jsjolund/sailoraid/report/Figures/Euler_angle.pdf

Yaw

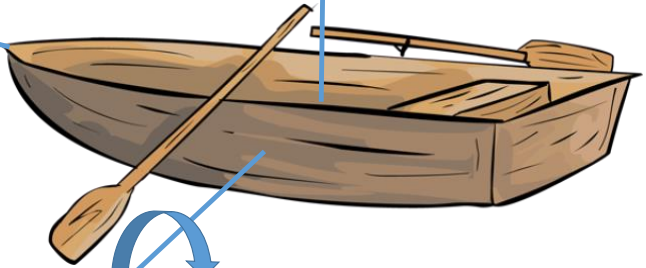
[picture p74: figure]

Pitch

Roll
