jsjolund/sailoraid/report/SourceFigures/linear.pdf

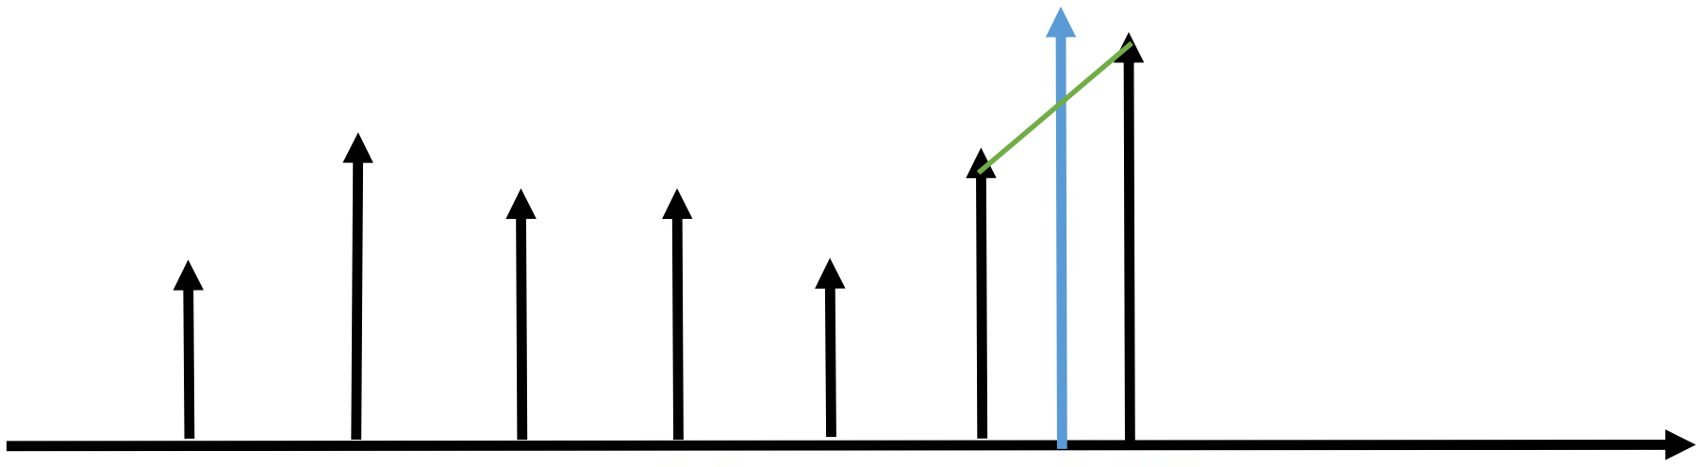
[picture p75: figure]
