jsjolund/sailoraid/Hardware/Mountingstation/Size of PCB.png

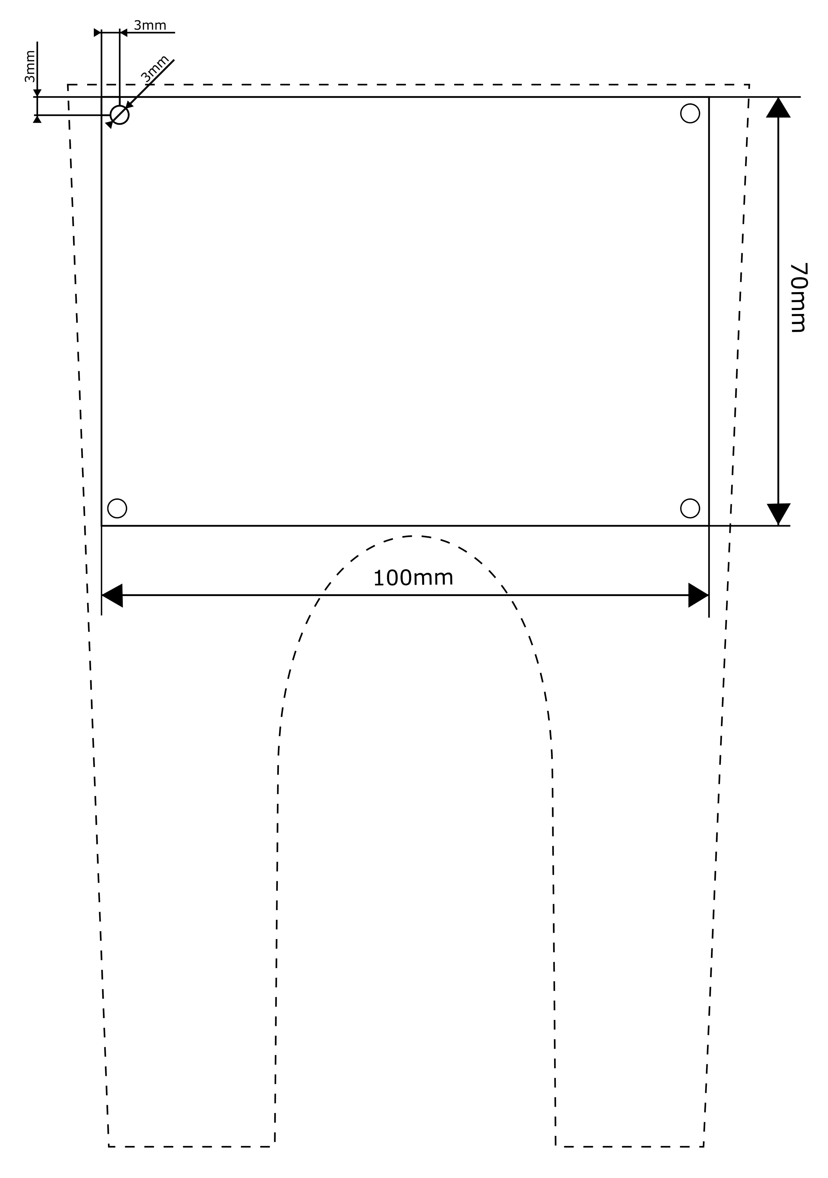
Hardware/Mountingstation/Size of PCB.png
