jsjolund/sailoraid/Presentationer/9/PCB_rev2_0.0.1.png

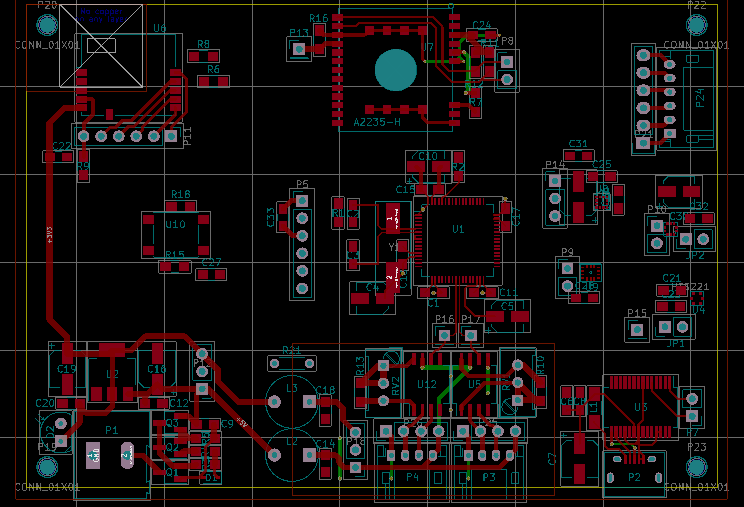
Presentationer/9/PCB_rev2_0.0.1.png
