jsjolund/sailoraid/Presentationer/11/pcb_rev2_Cu_tight.png

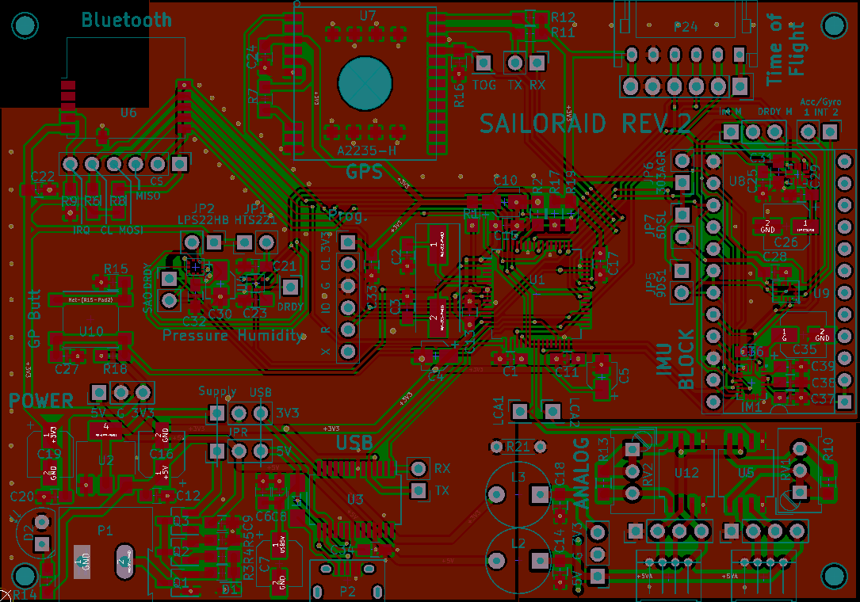
Presentationer/11/pcb_rev2_Cu_tight.png
