jsjolund/sailoraid/Presentationer/11/pcb_rev2_NoCu.png

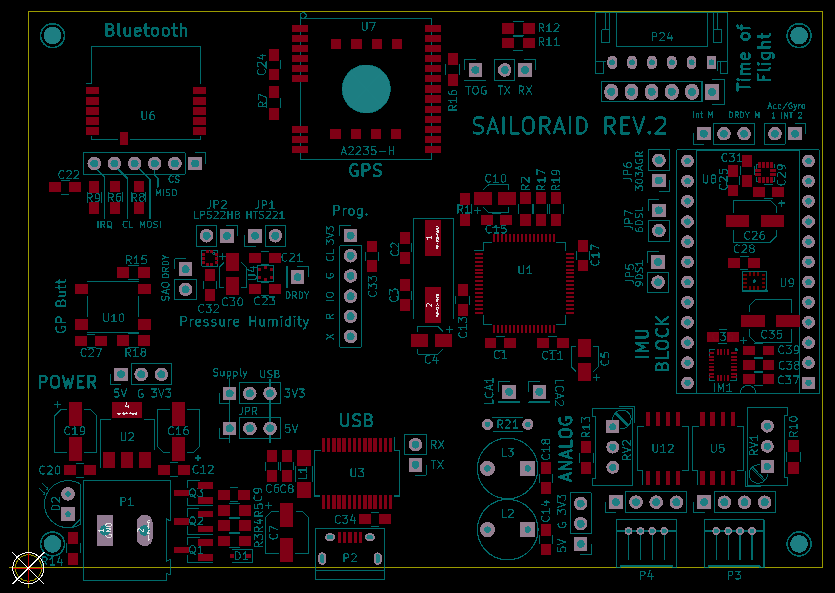
Presentationer/11/pcb_rev2_NoCu.png
