jsjolund/sailoraid/Presentationer/11/pcb_rev2_NoCu_decisions.png

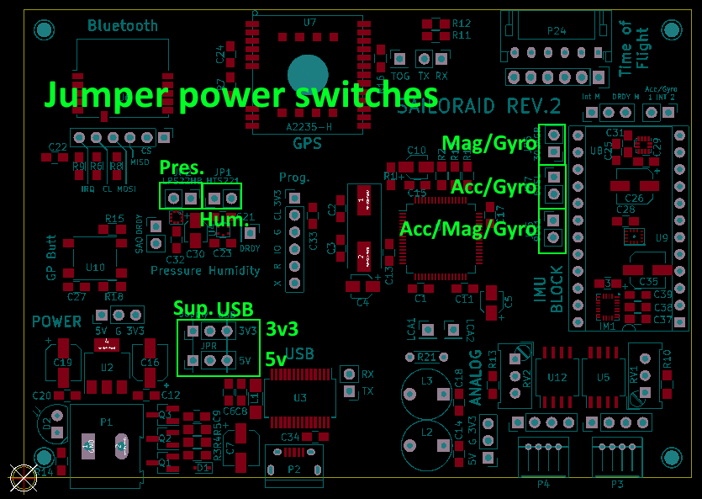
Presentationer/11/pcb_rev2_NoCu_decisions.png
