jsjolund/sailoraid/Presentationer/11/pcb_rev2_NoCu_eval.png

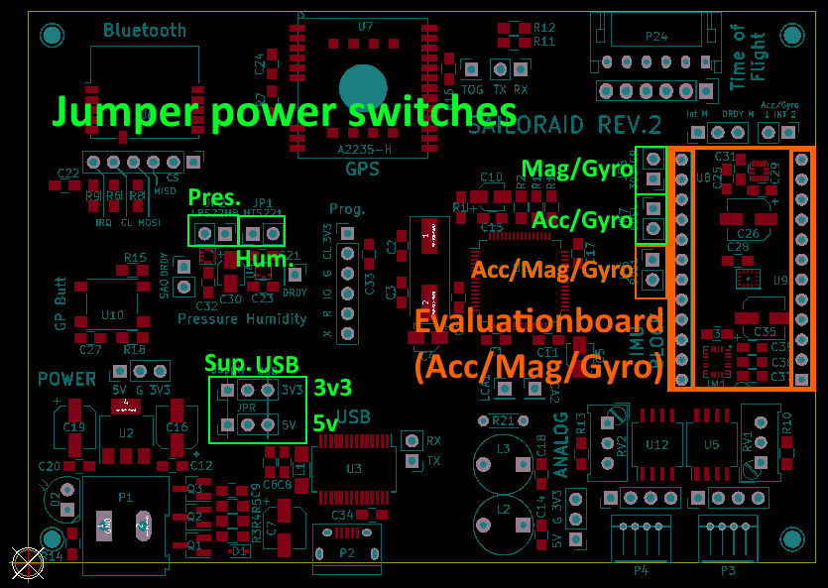
Presentationer/11/pcb_rev2_NoCu_eval.png
