jsjolund/sailoraid/Presentationer/11/pcb_rev2_NoCu_Marks.png

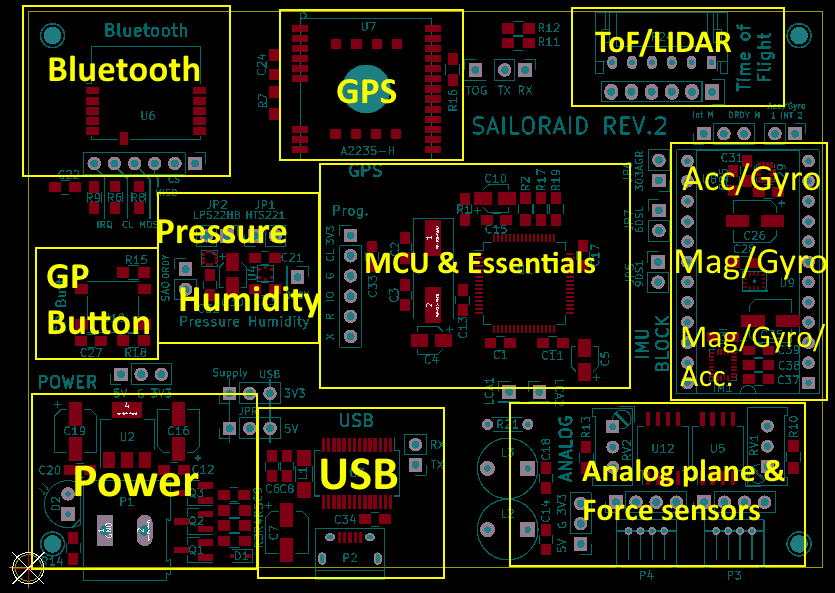
Presentationer/11/pcb_rev2_NoCu_Marks.png
