jsjolund/sailoraid/Presentationer/11/pcb_rev2_NoCu_meas.png

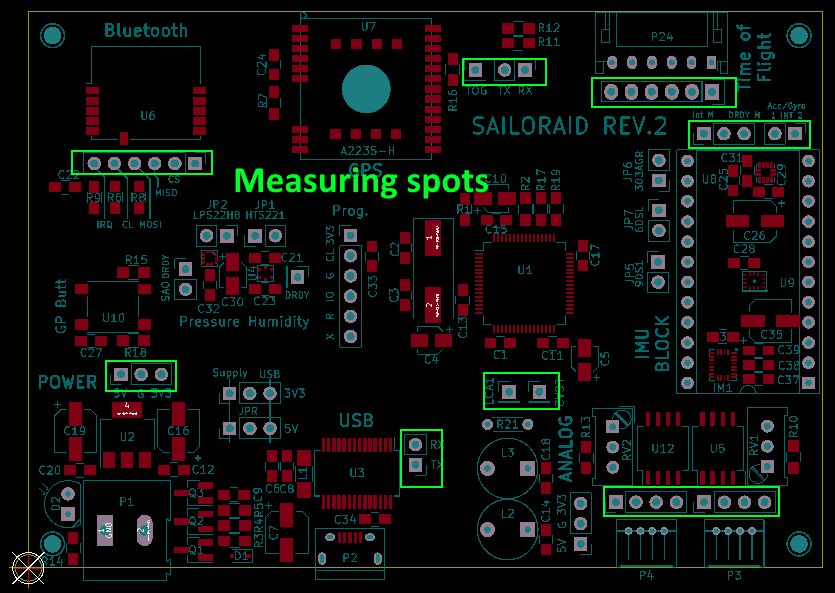
Presentationer/11/pcb_rev2_NoCu_meas.png
