jsjolund/sailoraid/Presentationer/11/pcb_rev2_NoCu_noeval.png

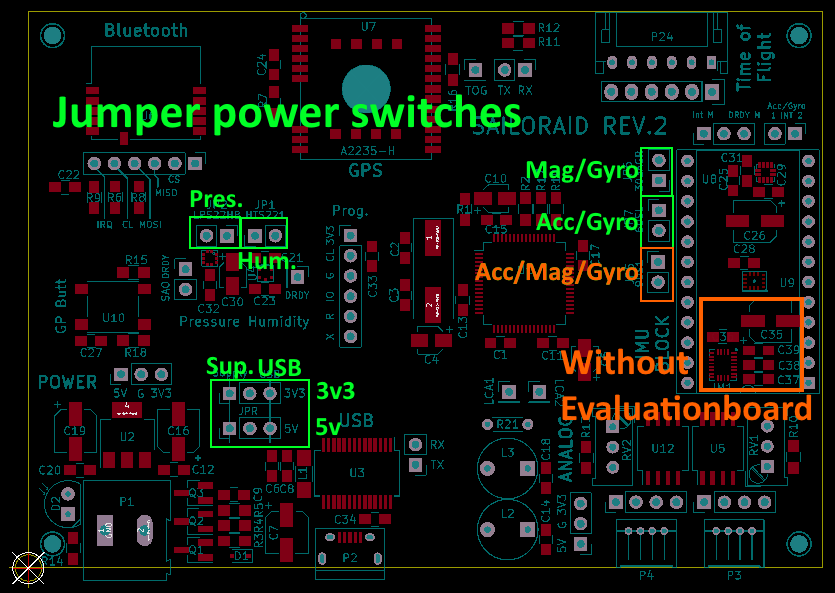
Presentationer/11/pcb_rev2_NoCu_noeval.png
