jsjolund/sailoraid/Presentationer/11/rev2_fitted.png

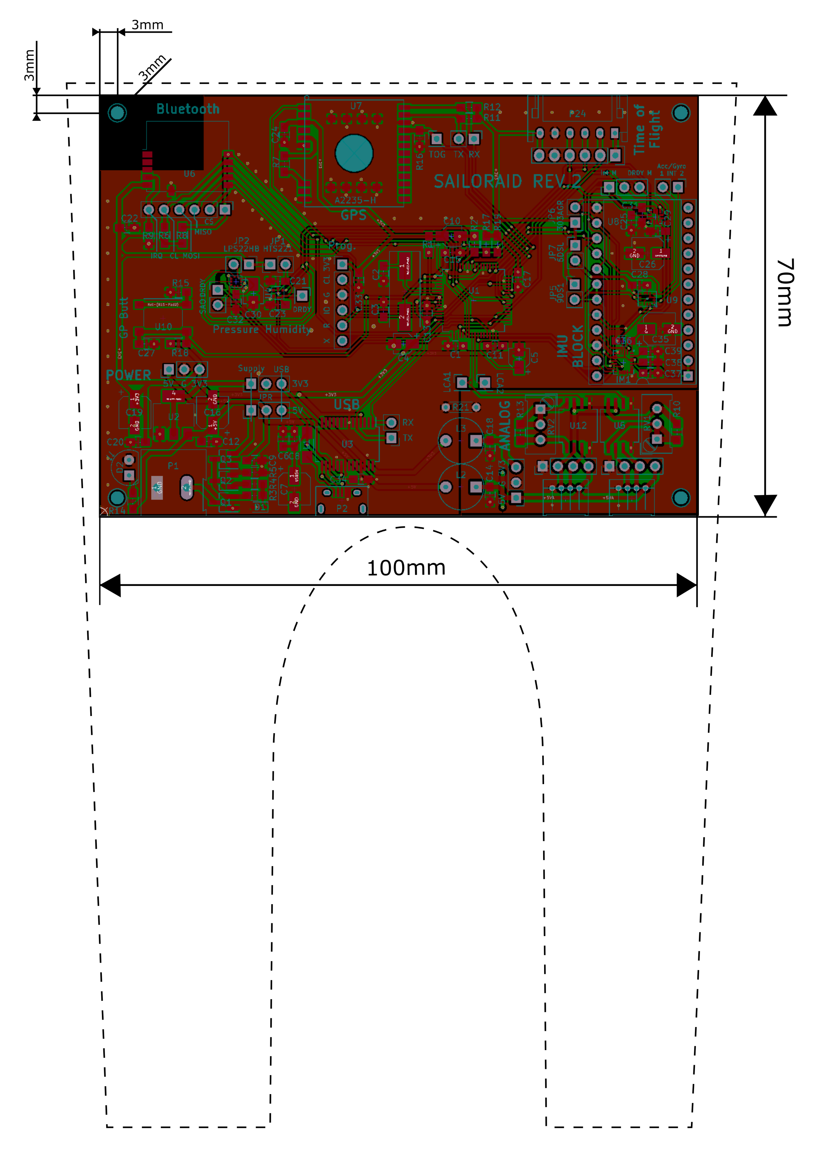
Presentationer/11/rev2_fitted.png
