jsjolund/sailoraid/Presentationer/Presentation 4/PCB_Annotated.png

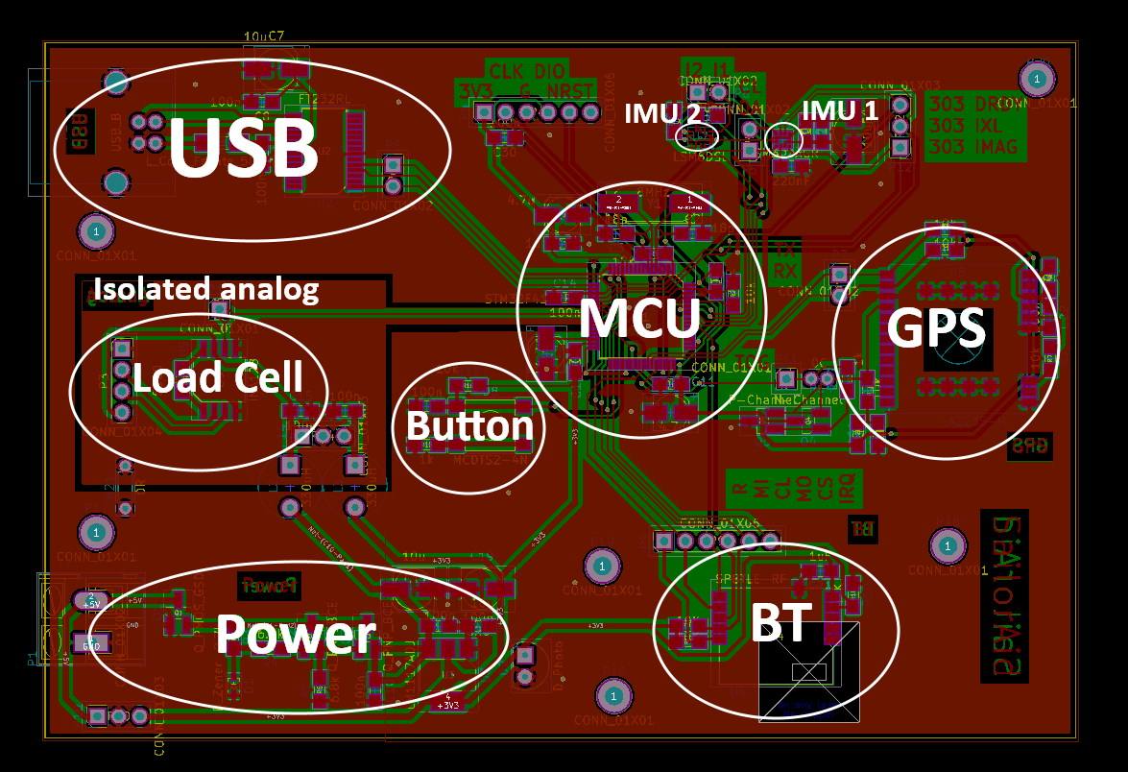
Presentationer/Presentation 4/PCB_Annotated.png
