jsjolund/sailoraid/Presentationer/Presentation 4/PCB_BAT_Note.png

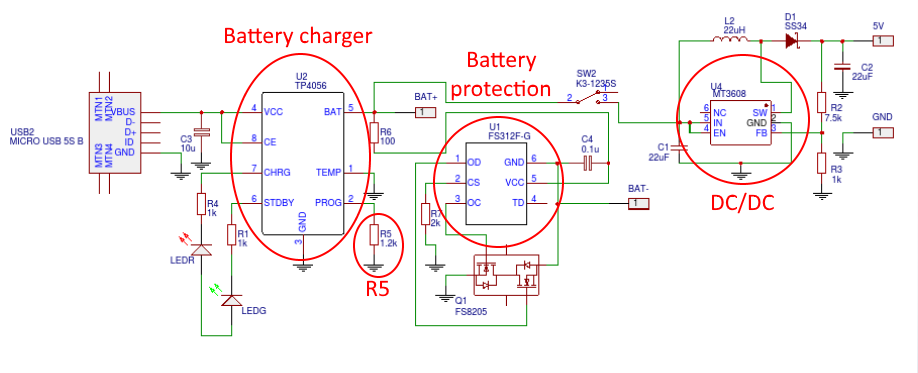
Presentationer/Presentation 4/PCB_BAT_Note.png
