jsjolund/sailoraid/Presentationer/Presentation 4/PCB_TN.png

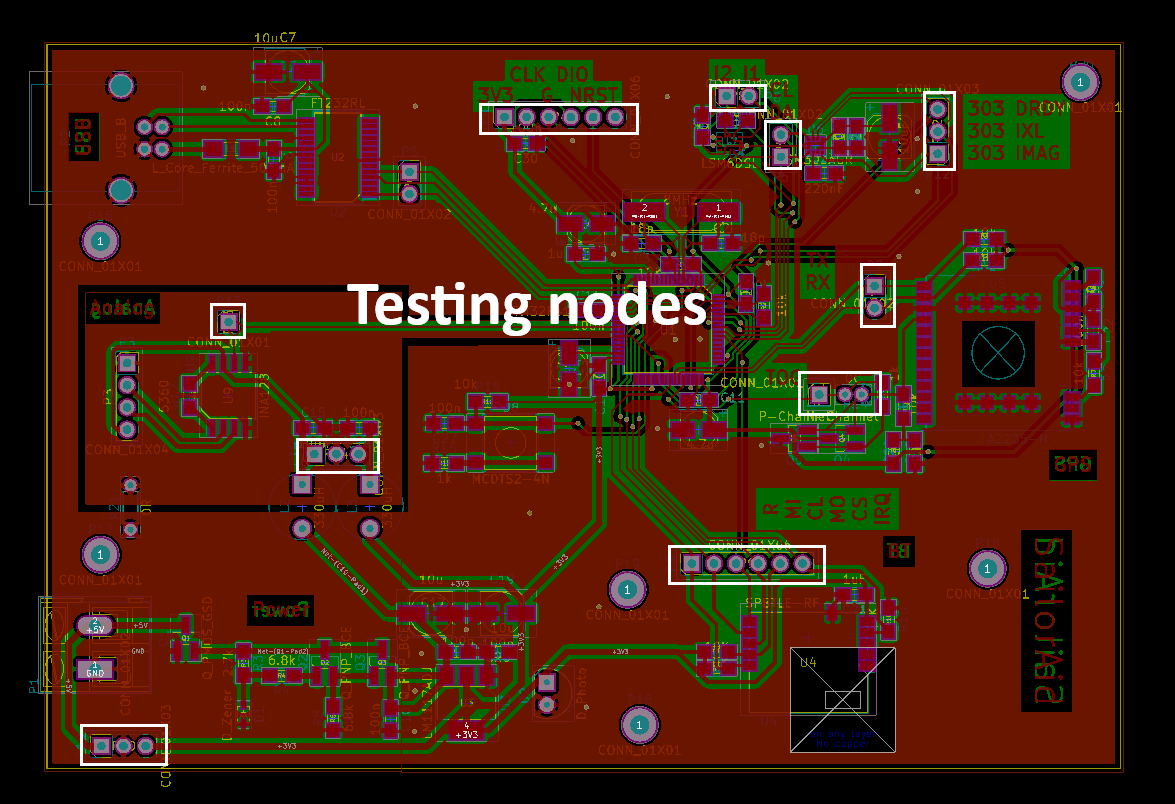
Presentationer/Presentation 4/PCB_TN.png
