jsjolund/sailoraid/Presentationer/Presentation 4/PCB_View.png

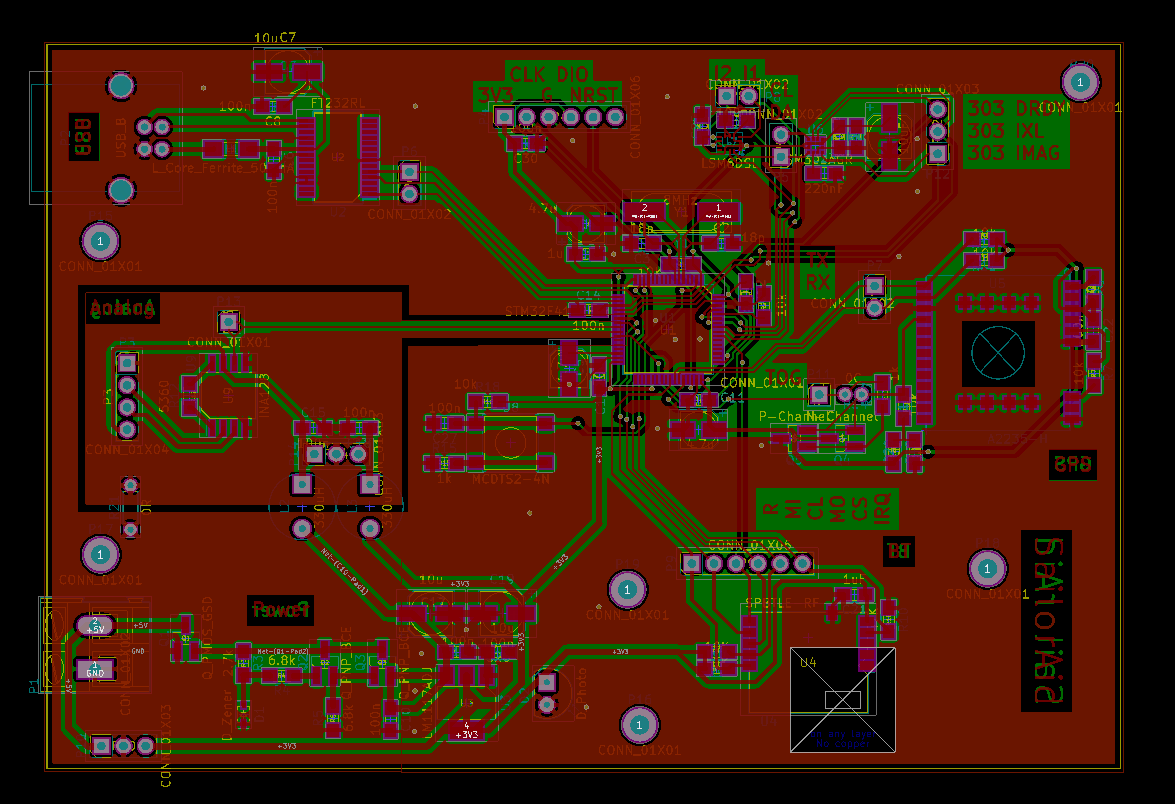
Presentationer/Presentation 4/PCB_View.png
