jsjolund/sailoraid/Presentationer/Presentation 4/schematic_General.png

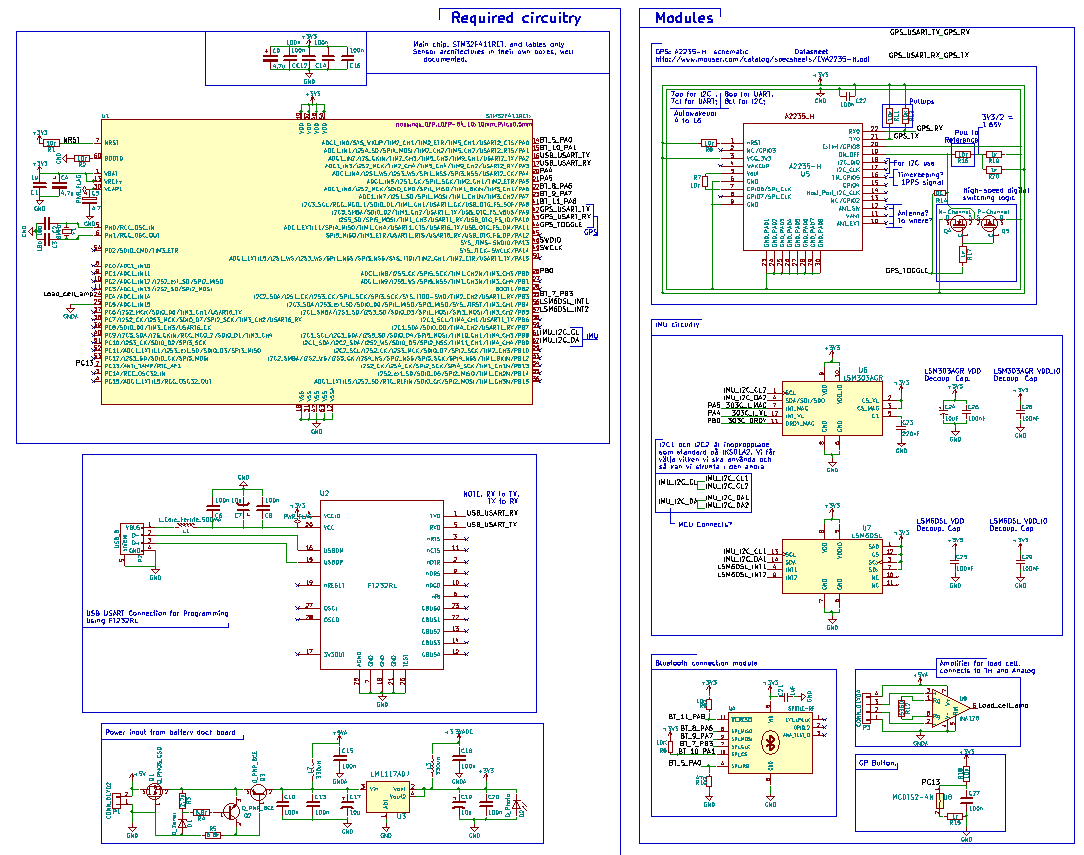
Presentationer/Presentation 4/schematic_General.png
