jsjolund/sailoraid/Presentationer/Presentation 4/schematic_General_note.png

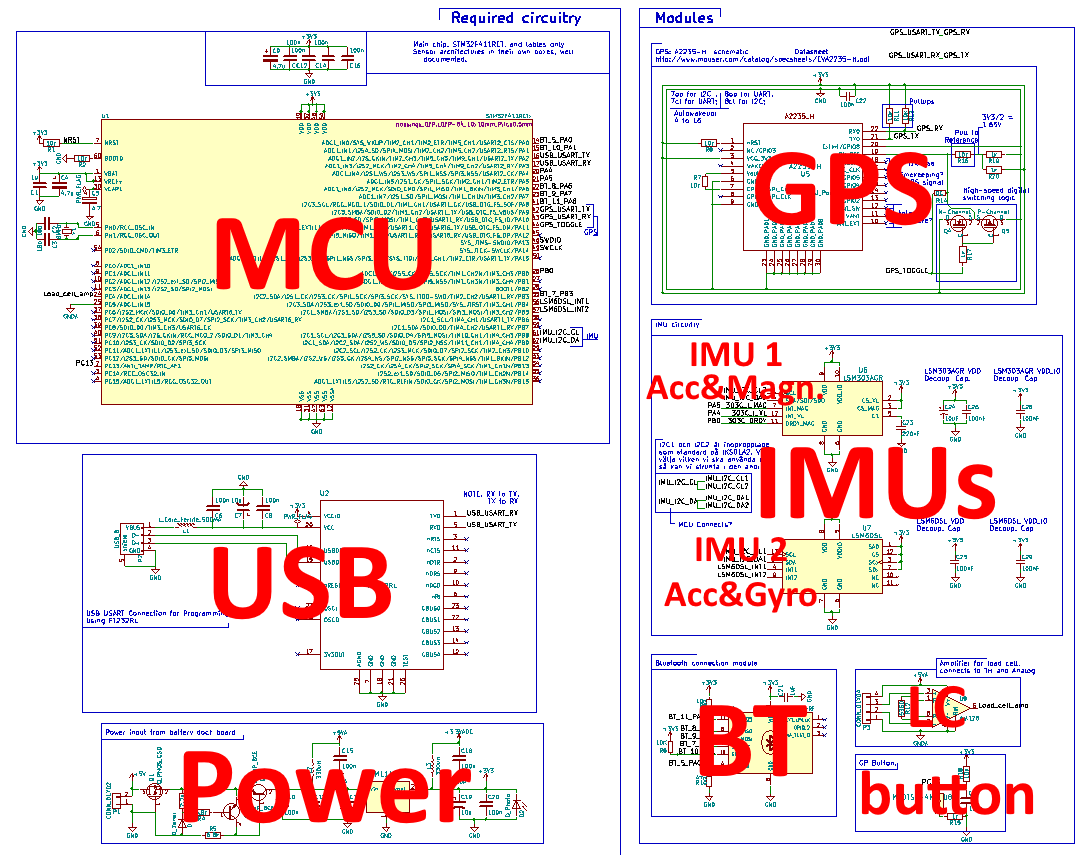
Presentationer/Presentation 4/schematic_General_note.png
