jsjolund/sailoraid/Presentationer/Presentation 4/schematic_MN.png

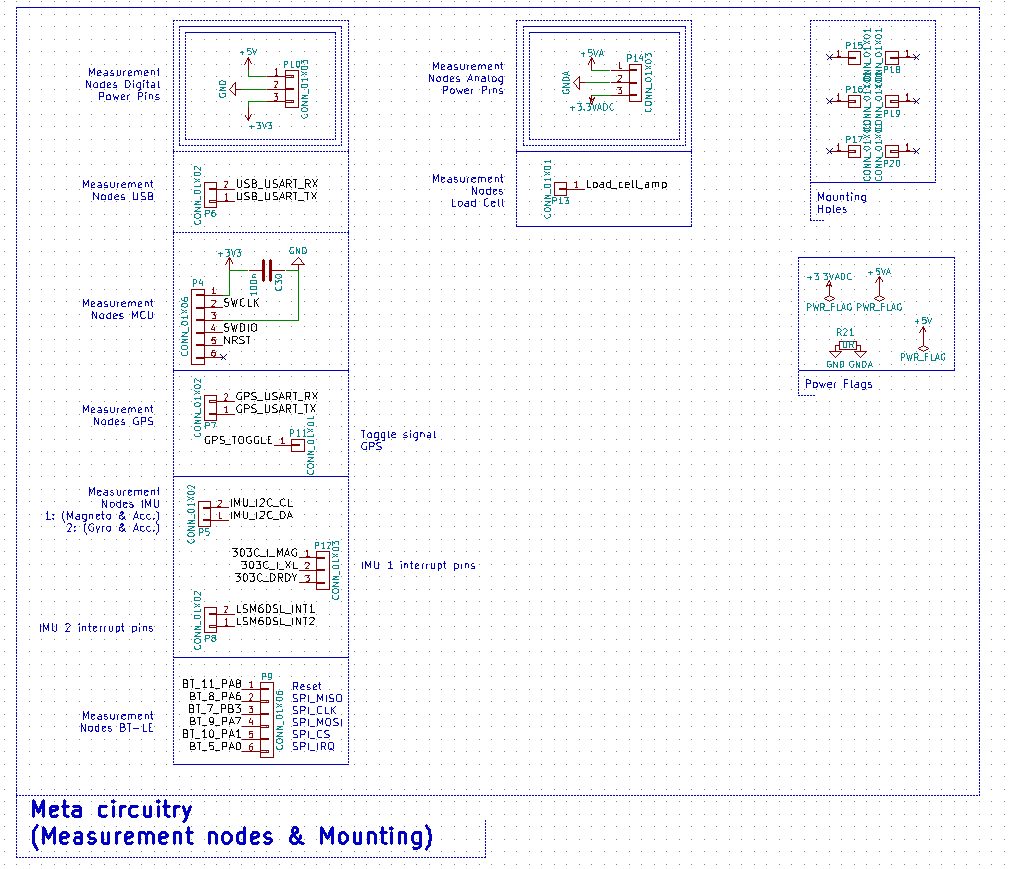
Presentationer/Presentation 4/schematic_MN.png
