jsjolund/sailoraid/Presentationer/Presentation 6/img/22359539_10154808777265474_2147093659_n.jpg

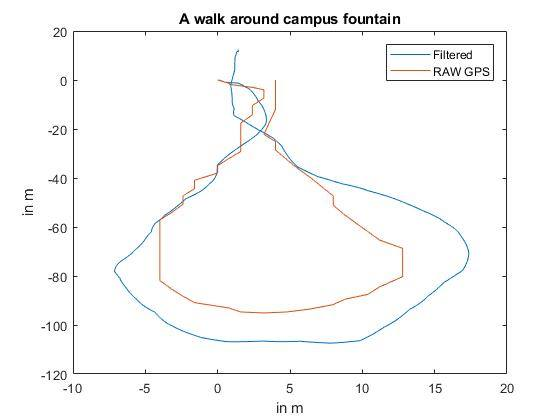
Presentationer/Presentation 6/img/22359539_10154808777265474_2147093659_n.jpg
