jsjolund/sailoraid/Presentationer/Presentation 6/img/log.png

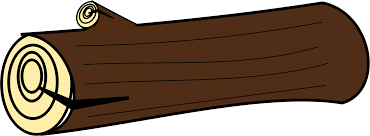
Presentationer/Presentation 6/img/log.png
