jsjolund/sailoraid/Presentationer/Presentation 6/img/low-battery-white-outline.png

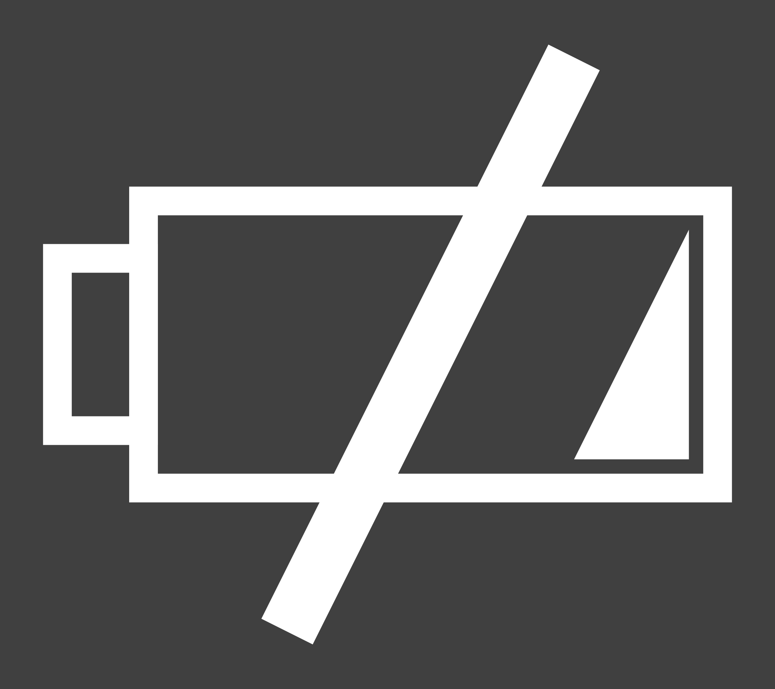
Presentationer/Presentation 6/img/low-battery-white-outline.png
