jsjolund/sailoraid/Presentationer/Presentation 6/img/Screenshot_20171006-211432.png

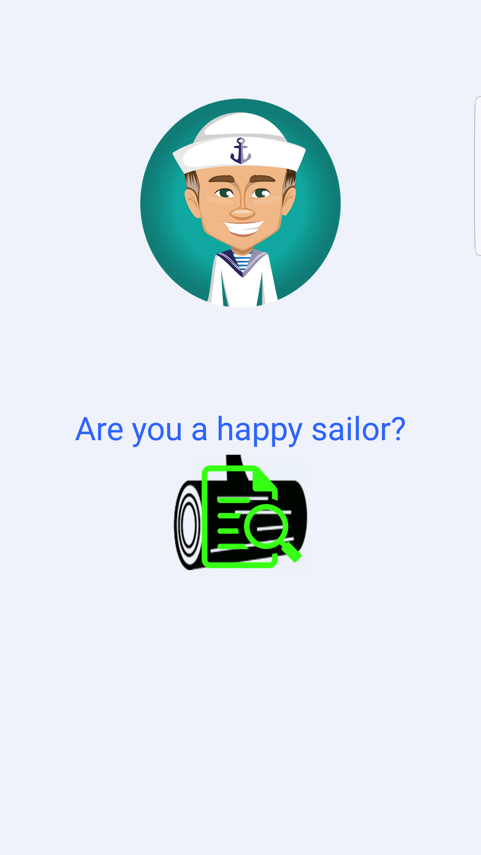
Presentationer/Presentation 6/img/Screenshot_20171006-211432.png
