jsjolund/sailoraid/Presentationer/Presentation 6/img/Screenshot_20171006-211447.png

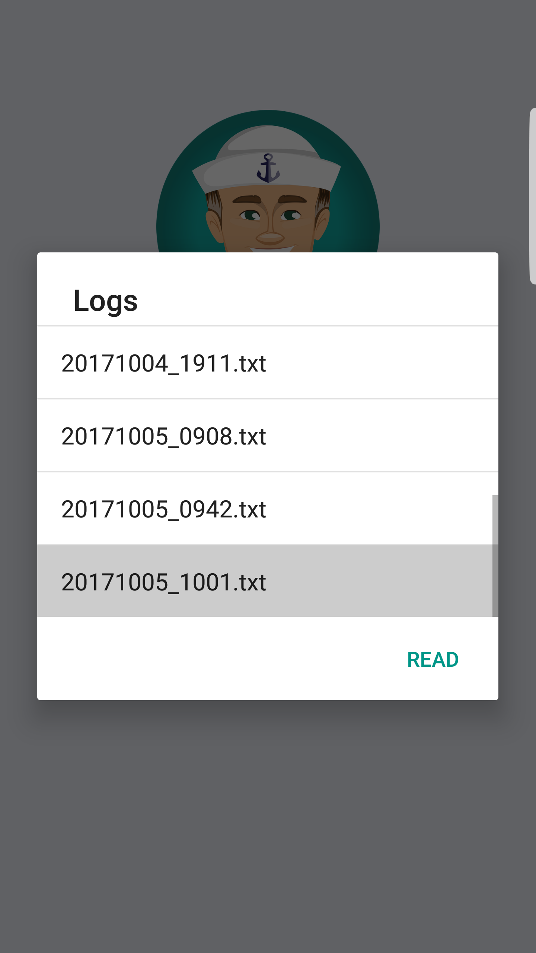
Presentationer/Presentation 6/img/Screenshot_20171006-211447.png
