jsjolund/sailoraid/Presentationer/Presentation 6/img/Screenshot_20171006-212822.png

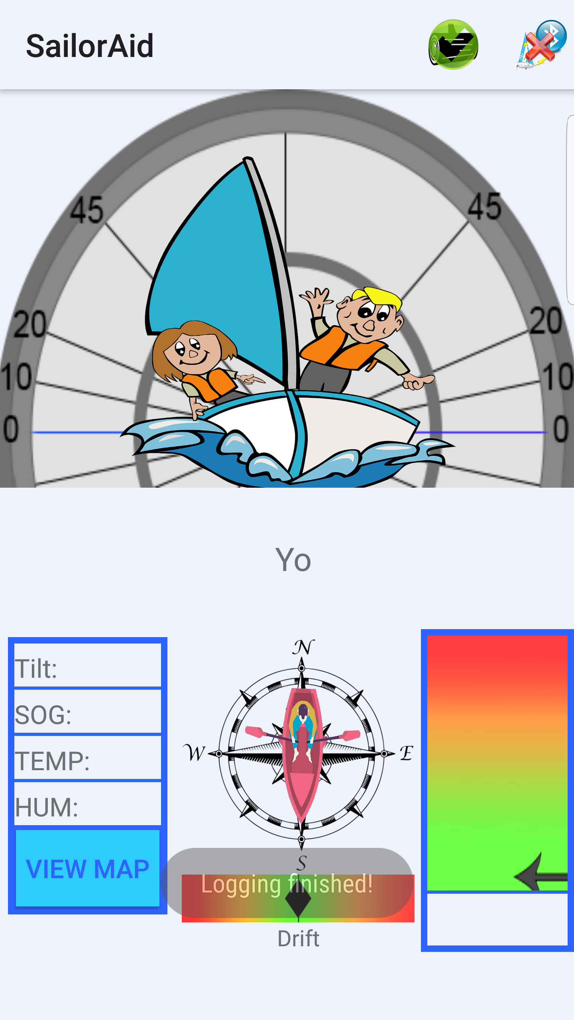
Presentationer/Presentation 6/img/Screenshot_20171006-212822.png
