jsjolund/sailoraid/Presentationer/Presentation 6/img/Screenshot_20171006-213508.png

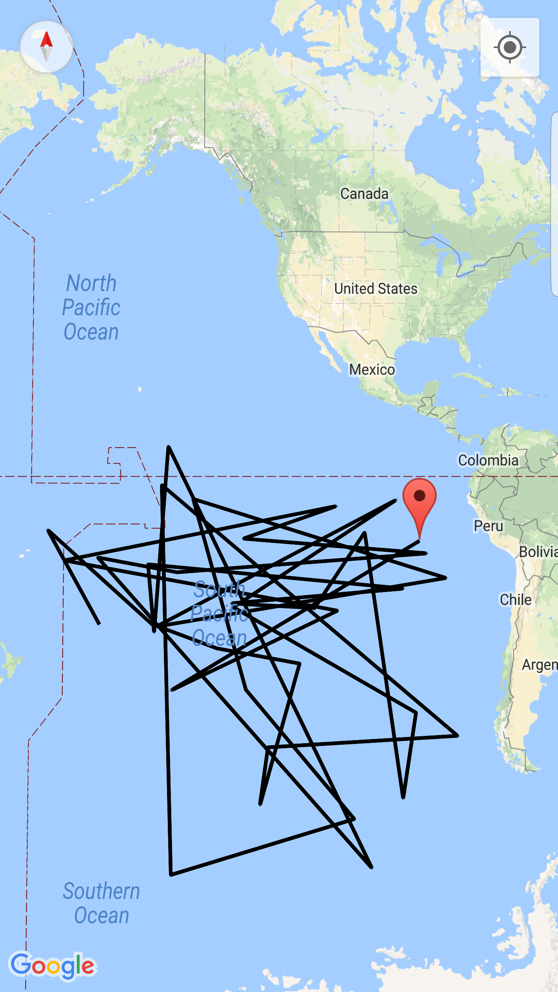
Presentationer/Presentation 6/img/Screenshot_20171006-213508.png
