jsjolund/sailoraid/Presentationer/Presentation 6/img/Screenshot_20171006-220036.png

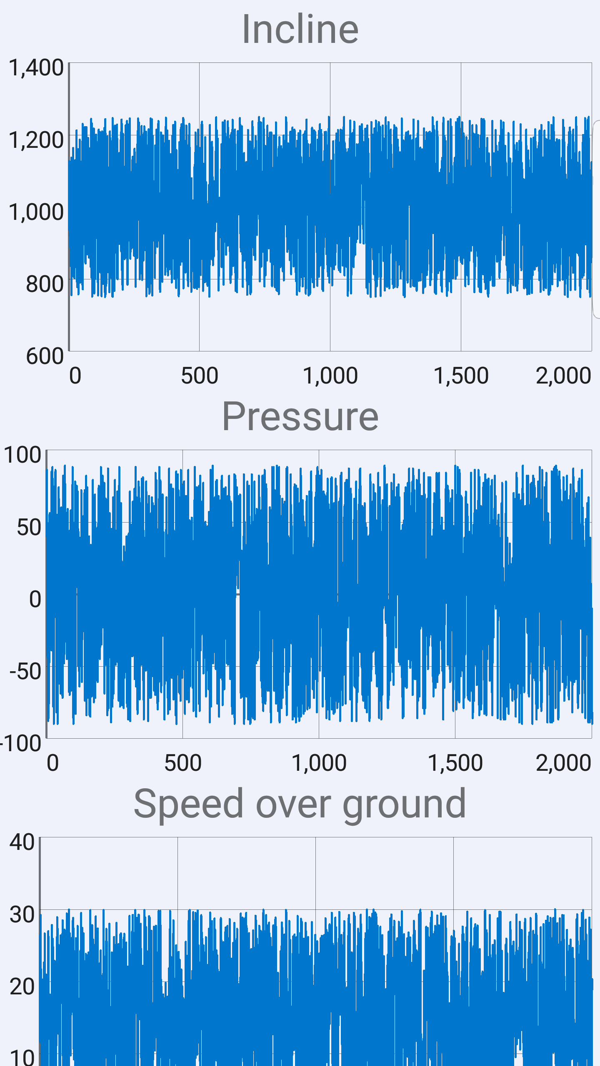
Presentationer/Presentation 6/img/Screenshot_20171006-220036.png
