jsjolund/sailoraid/Presentationer/Presentation 6/img/Screenshot_20171006-2115145.png

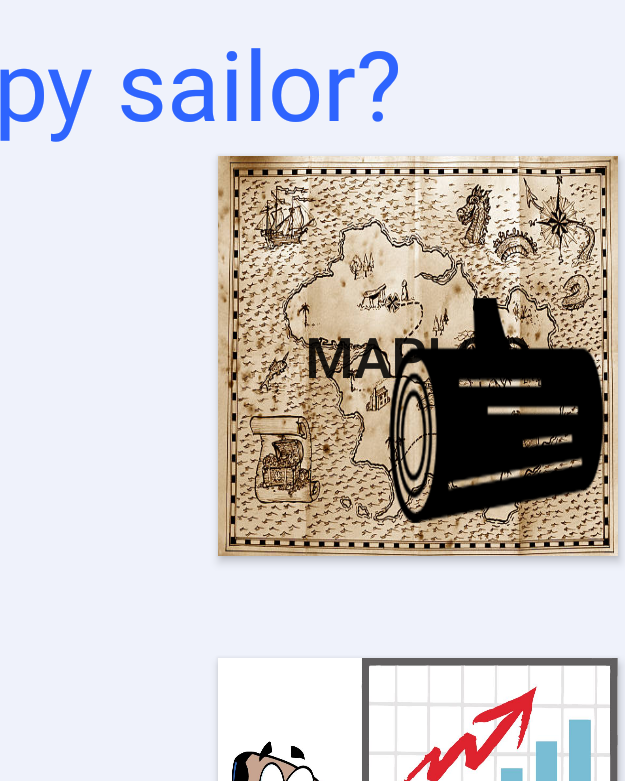
Presentationer/Presentation 6/img/Screenshot_20171006-2115145.png
