jsjolund/sailoraid/Presentationer/Presentation 7/Screenshot_20171013-161457.png

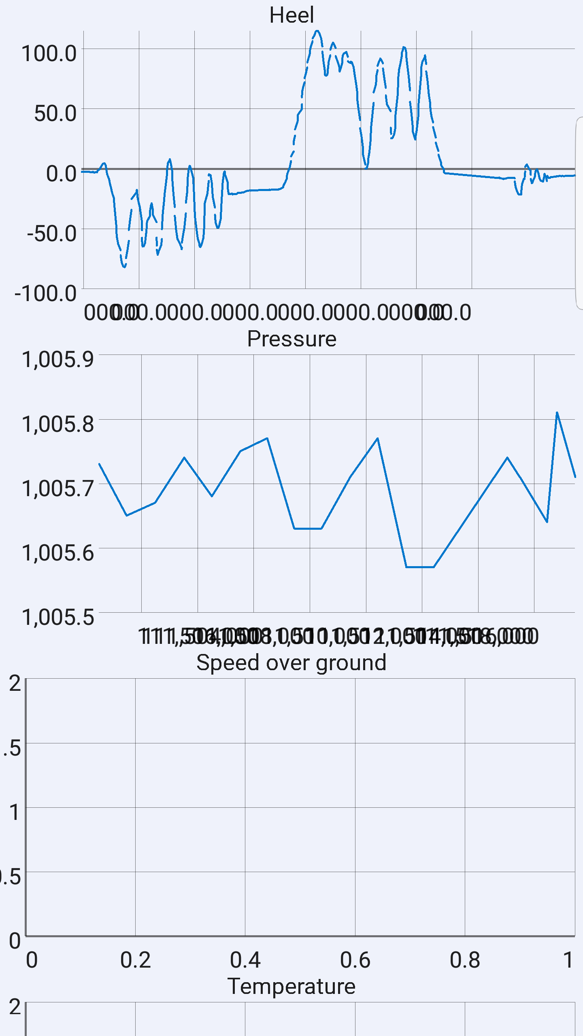
Presentationer/Presentation 7/Screenshot_20171013-161457.png
