jsjolund/sailoraid/Presentationer/Presentation 7/Screenshot_20171013-161503.png

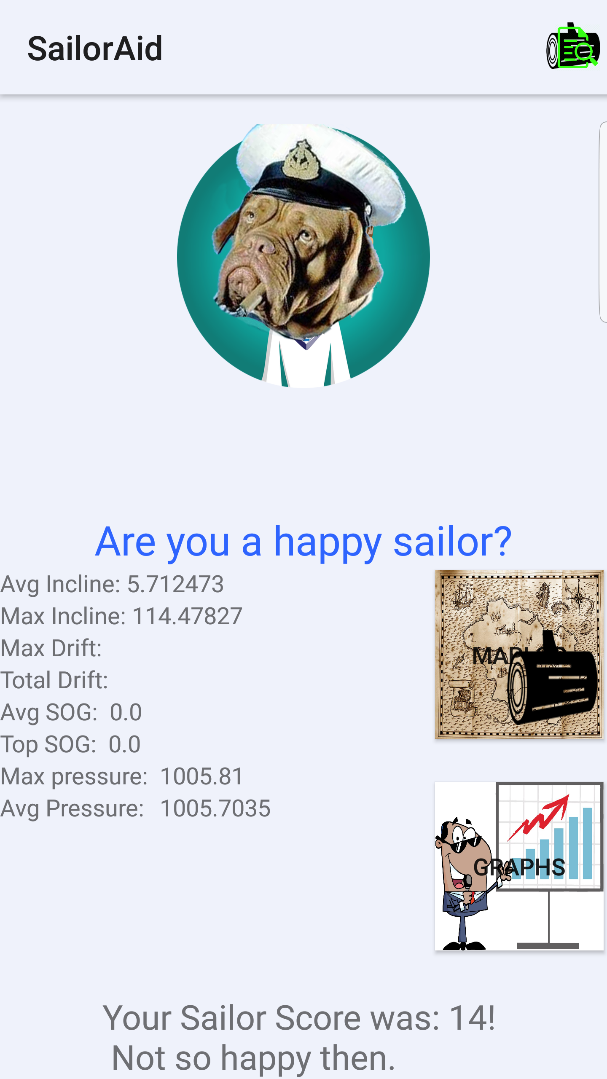
Presentationer/Presentation 7/Screenshot_20171013-161503.png
