jsjolund/sailoraid/Presentationer/Presentation 10/3e073e2acaca0a635fb6824c3f5e855d.jpg

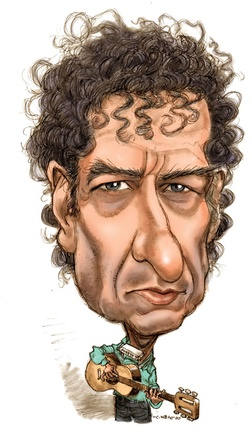
Presentationer/Presentation 10/3e073e2acaca0a635fb6824c3f5e855d.jpg
