jsjolund/sailoraid/Presentationer/Presentation 10/4.jpg

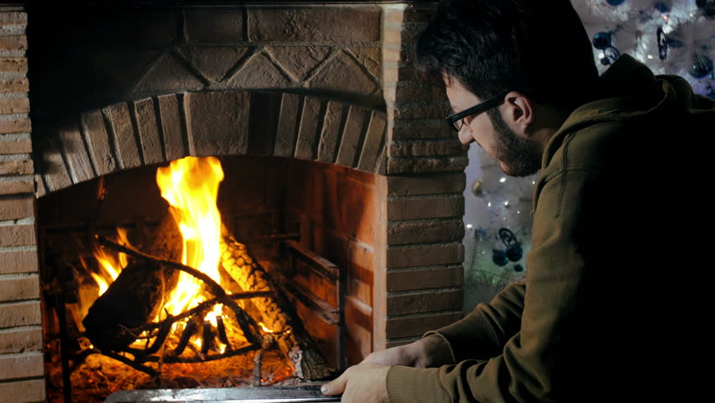
Presentationer/Presentation 10/4.jpg
