jsjolund/sailoraid/Presentationer/Presentation 10/70ce21d3d8f3dff4c3a7d7f7be6c27f0.jpg

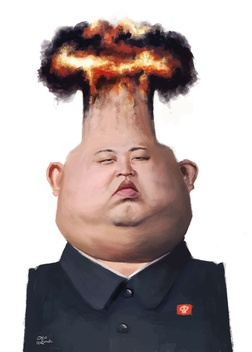
Presentationer/Presentation 10/70ce21d3d8f3dff4c3a7d7f7be6c27f0.jpg
