jsjolund/sailoraid/Presentationer/Presentation 10/800px-6DOF_en.jpg

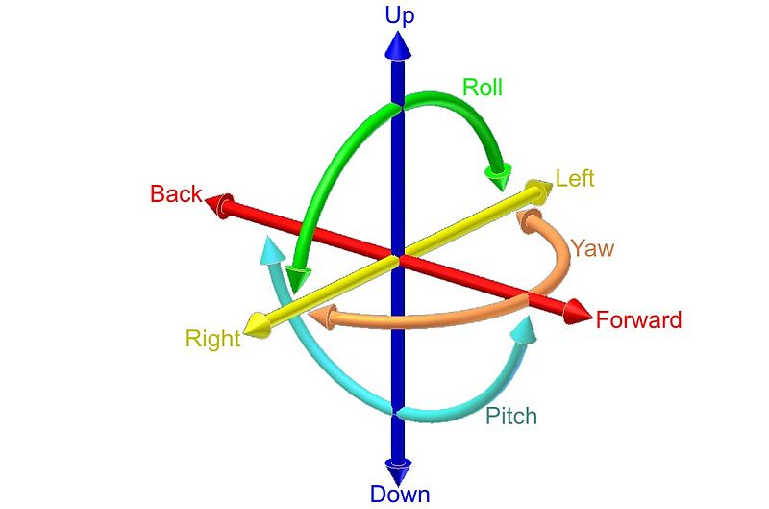
Presentationer/Presentation 10/800px-6DOF_en.jpg
