jsjolund/sailoraid/Presentationer/Presentation 10/612938.jpg

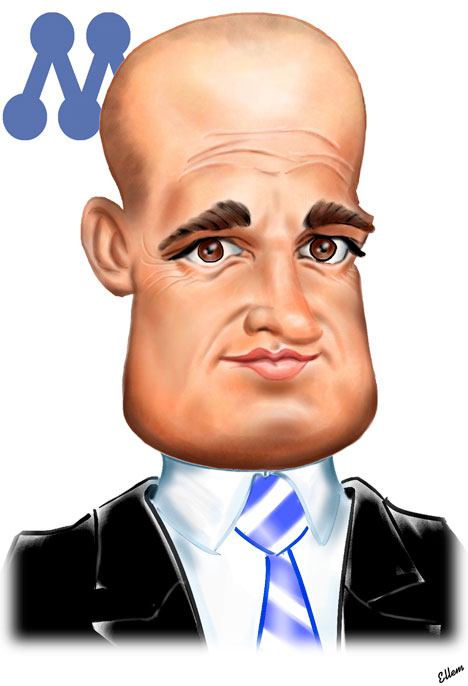
Presentationer/Presentation 10/612938.jpg
