jsjolund/sailoraid/Presentationer/Presentation 10/1355927.jpg

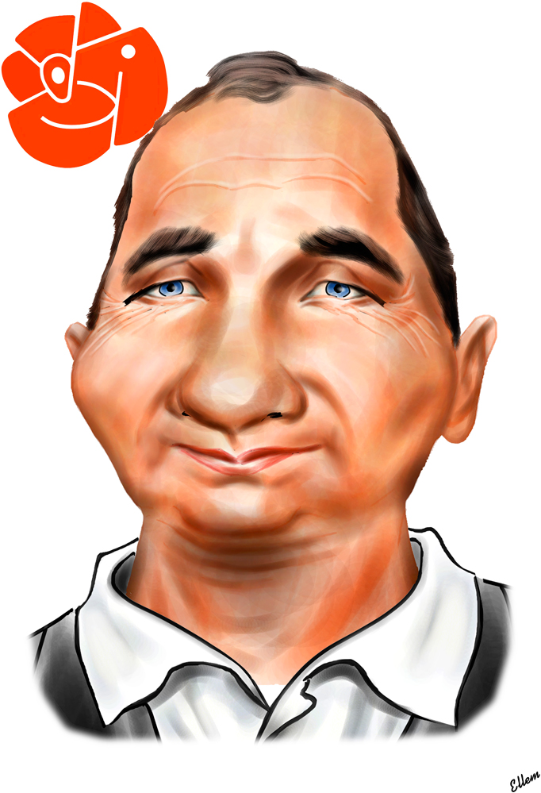
Presentationer/Presentation 10/1355927.jpg
