jsjolund/sailoraid/Presentationer/Presentation 10/20171110_090245.png

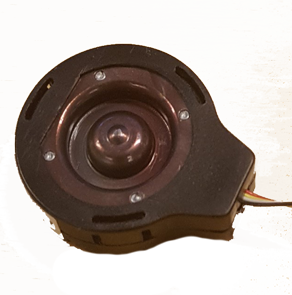
Presentationer/Presentation 10/20171110_090245.png
