jsjolund/sailoraid/Presentationer/Presentation 10/63510876177064812534_thumb190.jpg

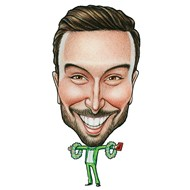
Presentationer/Presentation 10/63510876177064812534_thumb190.jpg
