jsjolund/sailoraid/Presentationer/Presentation 10/63510876297606224254_thumb190.jpg

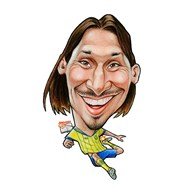
Presentationer/Presentation 10/63510876297606224254_thumb190.jpg
