jsjolund/sailoraid/Presentationer/Presentation 10/altecnic-pressure-gauge-010-bar-14-02200936L.jpg

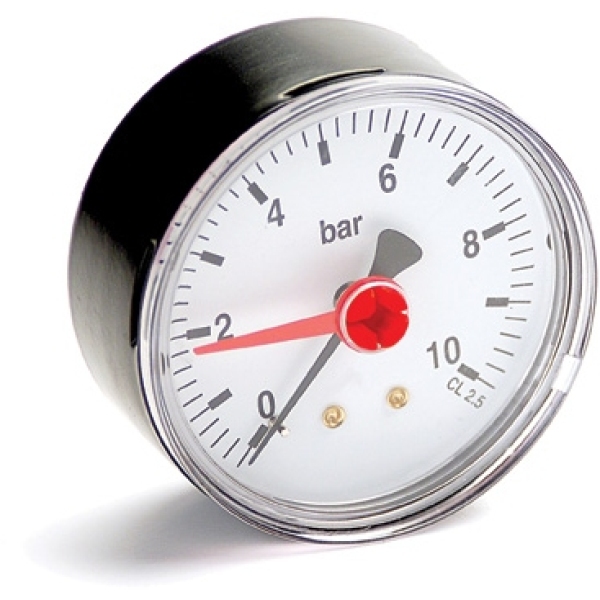
Presentationer/Presentation 10/altecnic-pressure-gauge-010-bar-14-02200936L.jpg
