jsjolund/sailoraid/Presentationer/Presentation 10/anonym_157392347.jpg

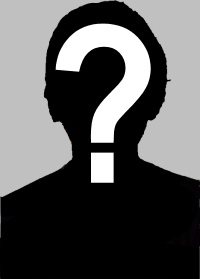
Presentationer/Presentation 10/anonym_157392347.jpg
