jsjolund/sailoraid/Presentationer/Presentation 10/Audio.png

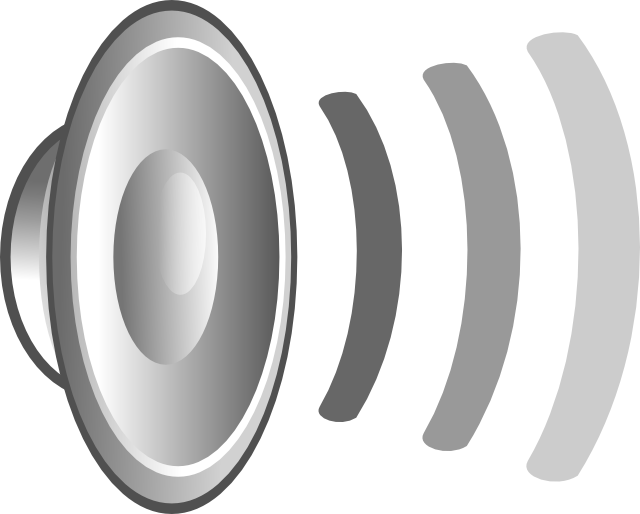
Presentationer/Presentation 10/Audio.png
