jsjolund/sailoraid/Presentationer/Presentation 10/brain.ngsversion.1398176967716.png

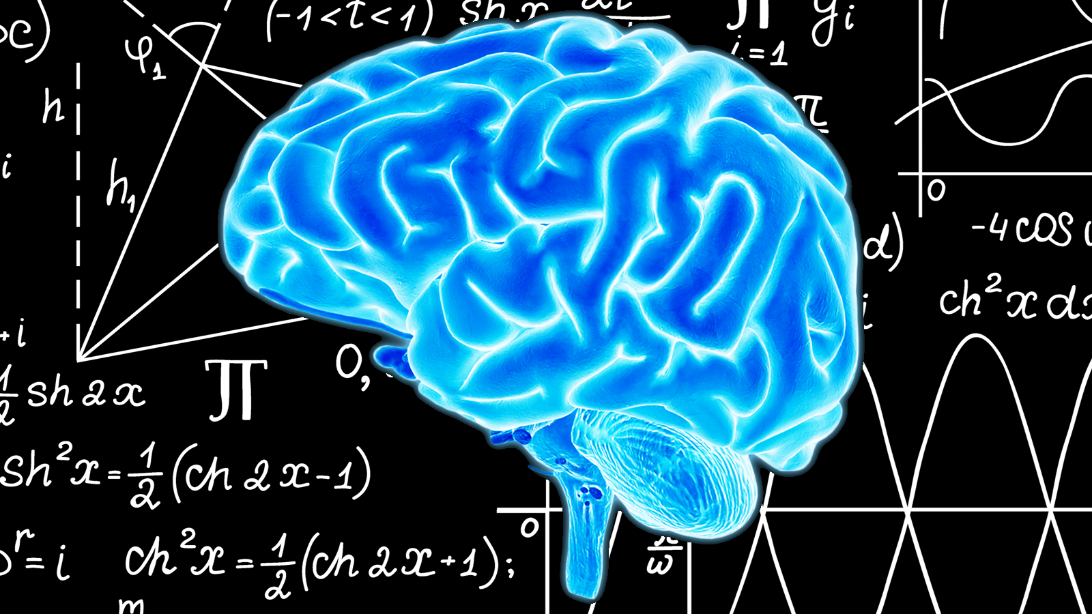
Presentationer/Presentation 10/brain.ngsversion.1398176967716.png
