jsjolund/sailoraid/Presentationer/Presentation 10/bt.png

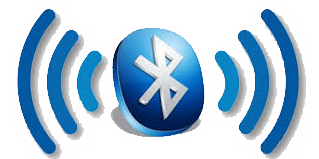
Presentationer/Presentation 10/bt.png
