jsjolund/sailoraid/Presentationer/Presentation 10/f8bc2516c1abe9594e8770406cbdeb14.jpg

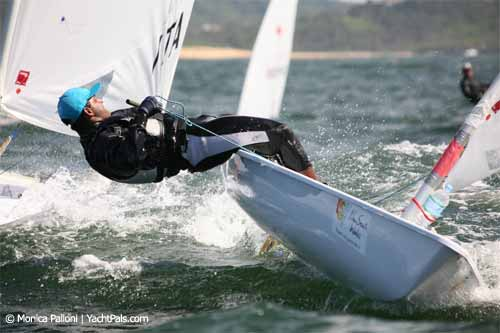
Presentationer/Presentation 10/f8bc2516c1abe9594e8770406cbdeb14.jpg
