jsjolund/sailoraid/Presentationer/Presentation 10/Filip-Hammar-2.jpg

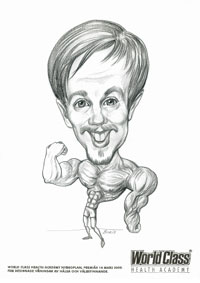
Presentationer/Presentation 10/Filip-Hammar-2.jpg
