jsjolund/sailoraid/Presentationer/Presentation 10/johannes.jpg

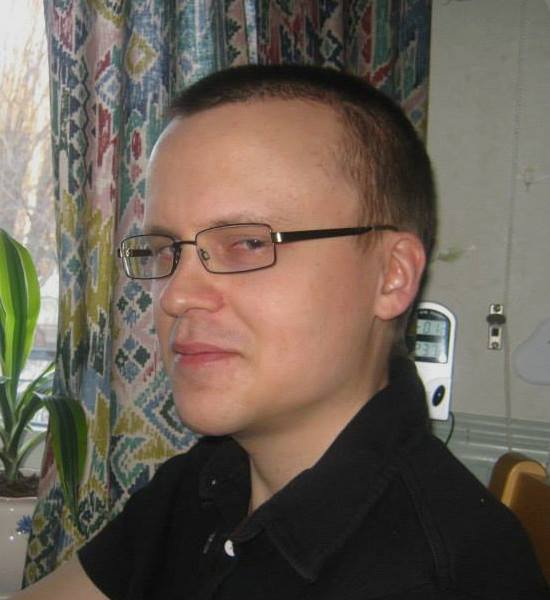
Presentationer/Presentation 10/johannes.jpg
