jsjolund/sailoraid/Presentationer/Presentation 10/karikatyr-av-presidentkandidaten-donald-trump-70328509.jpg

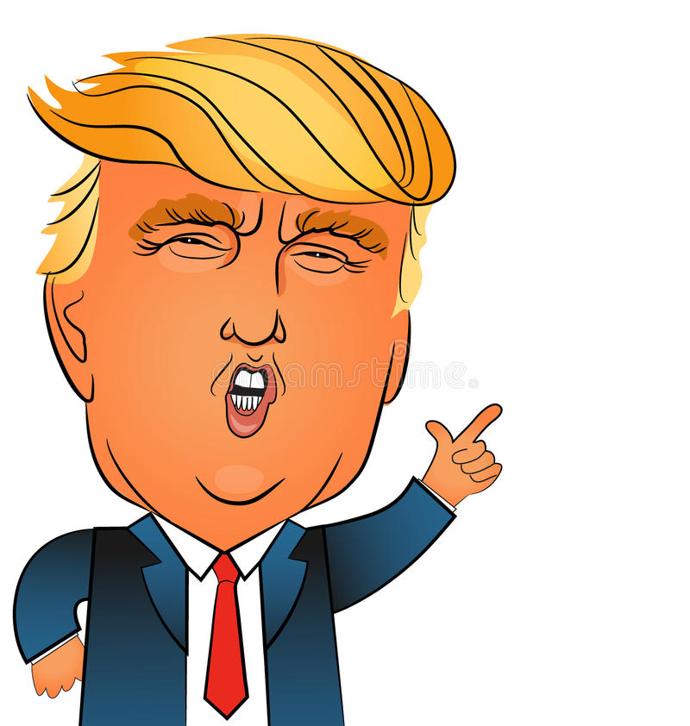
Presentationer/Presentation 10/karikatyr-av-presidentkandidaten-donald-trump-70328509.jpg
