jsjolund/sailoraid/Presentationer/Presentation 10/ladda ned (1).jpg

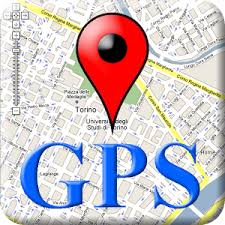
Presentationer/Presentation 10/ladda ned (1).jpg
