jsjolund/sailoraid/Presentationer/Presentation 10/ladda ned (2).jpg

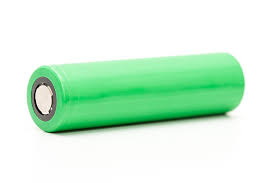
Presentationer/Presentation 10/ladda ned (2).jpg
