jsjolund/sailoraid/Presentationer/Presentation 10/ladda ned (2).png

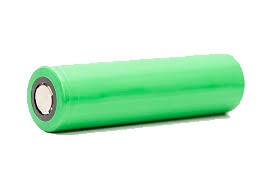
Presentationer/Presentation 10/ladda ned (2).png
