jsjolund/sailoraid/Presentationer/Presentation 10/noise-and-vibration.png

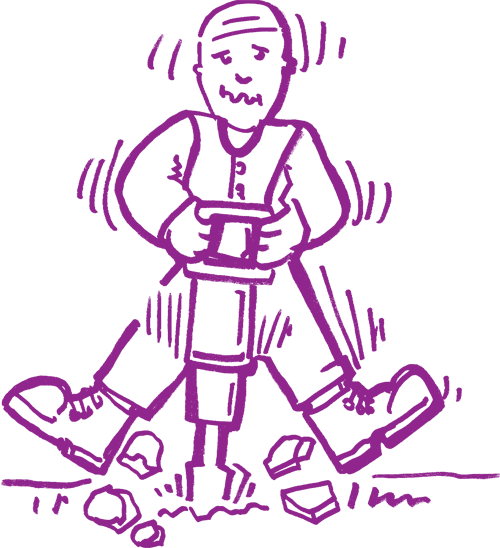
Presentationer/Presentation 10/noise-and-vibration.png
