jsjolund/sailoraid/Presentationer/Presentation 10/phone2.png

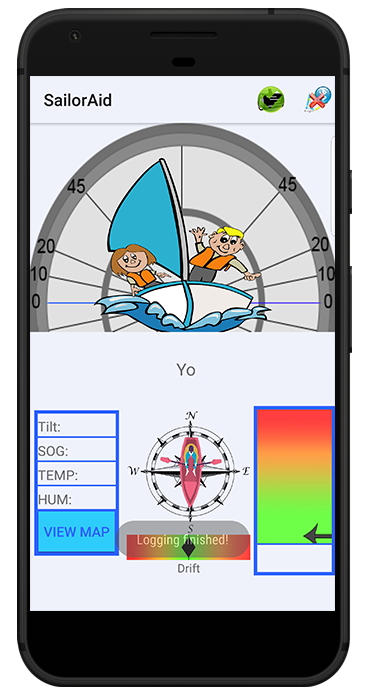
Presentationer/Presentation 10/phone2.png
