jsjolund/sailoraid/Presentationer/Presentation 10/phone-pixel-black_1x.png

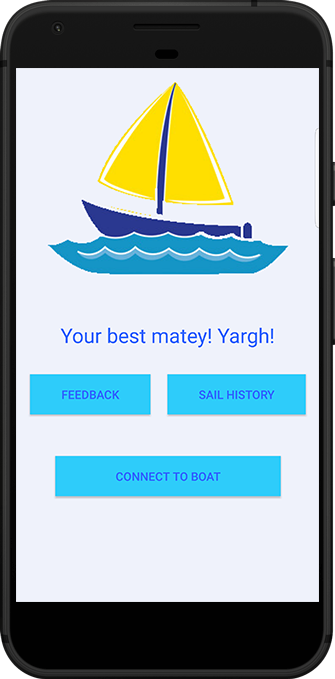
Presentationer/Presentation 10/phone-pixel-black_1x.png
