jsjolund/sailoraid/Presentationer/Presentation 10/pico.jpg

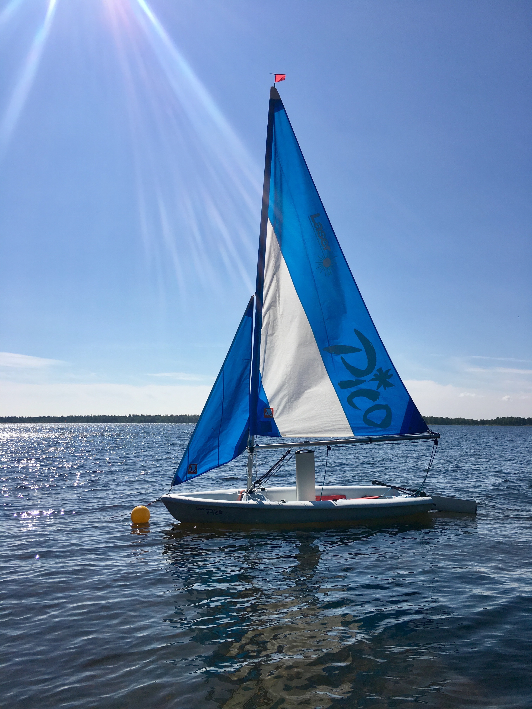
Presentationer/Presentation 10/pico.jpg
