jsjolund/sailoraid/Presentationer/Presentation 10/pico_center.png

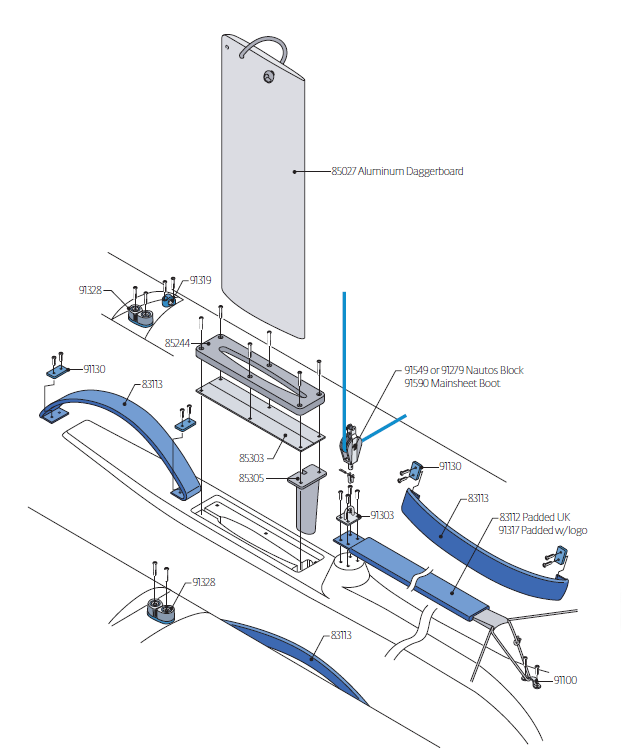
Presentationer/Presentation 10/pico_center.png
