jsjolund/sailoraid/Presentationer/Presentation 10/Points_of_sail--English-heart.jpg

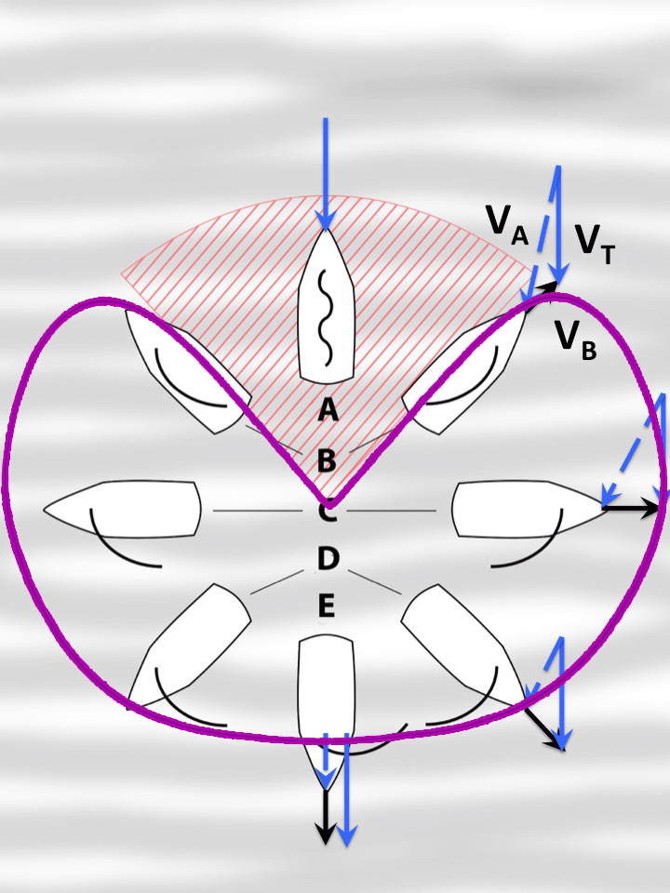
Presentationer/Presentation 10/Points_of_sail--English-heart.jpg
