jsjolund/sailoraid/Presentationer/Presentation 10/Screenshot_20171120-170956.png

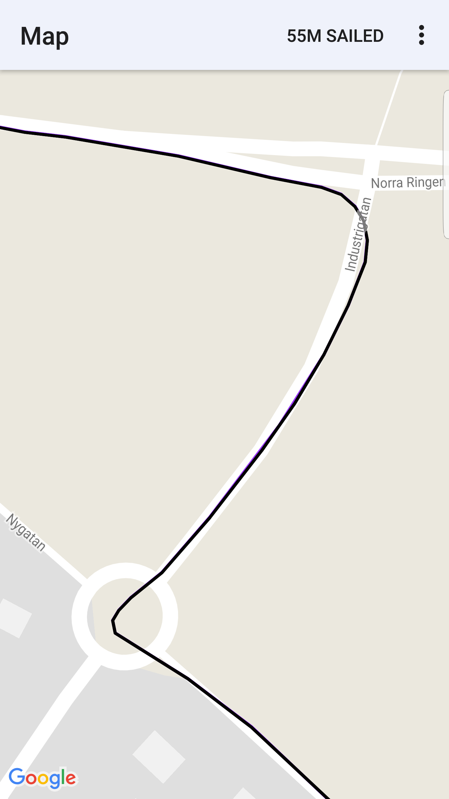
Presentationer/Presentation 10/Screenshot_20171120-170956.png
