jsjolund/sailoraid/Presentationer/Presentation 10/Screenshot_20171120-171015.png

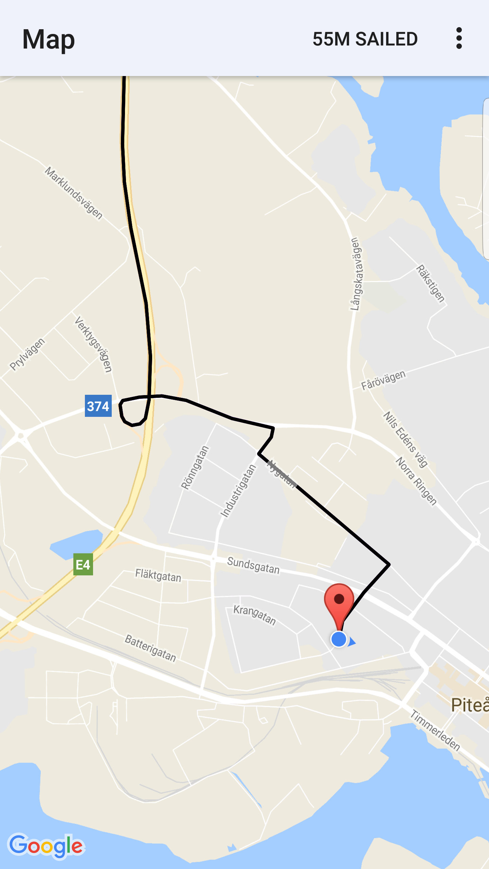
Presentationer/Presentation 10/Screenshot_20171120-171015.png
