jsjolund/sailoraid/Presentationer/Presentation 10/Screenshot_20171123-202154.png

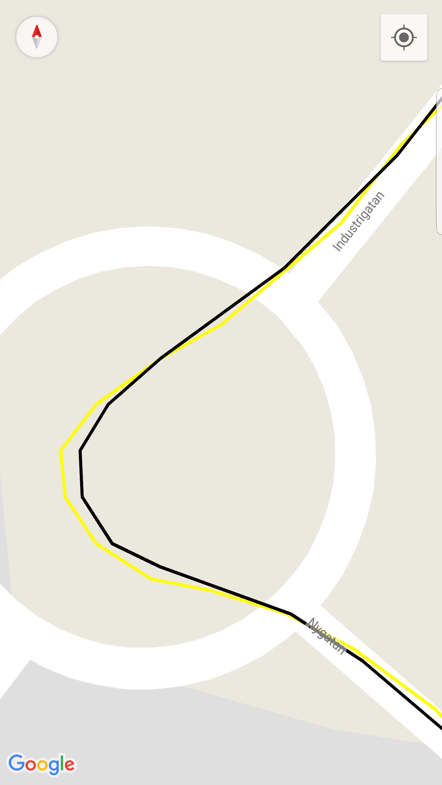
Presentationer/Presentation 10/Screenshot_20171123-202154.png
