jsjolund/sailoraid/Presentationer/Presentation 10/Screenshot_20171126-105507.png

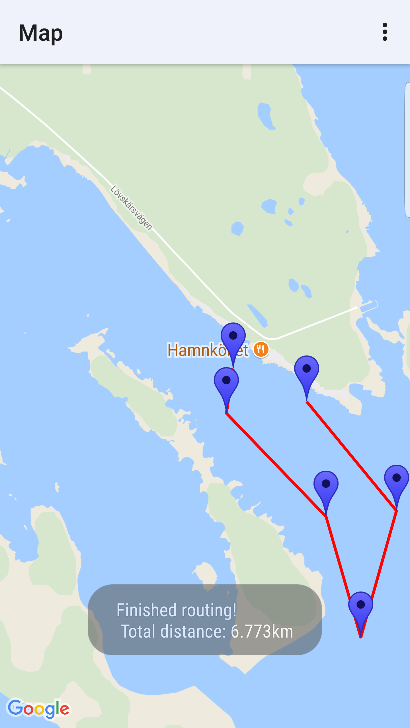
Presentationer/Presentation 10/Screenshot_20171126-105507.png
