jsjolund/sailoraid/Presentationer/Presentation 10/u8-black-bingo-original-imaeeftzbhffagvw.jpeg

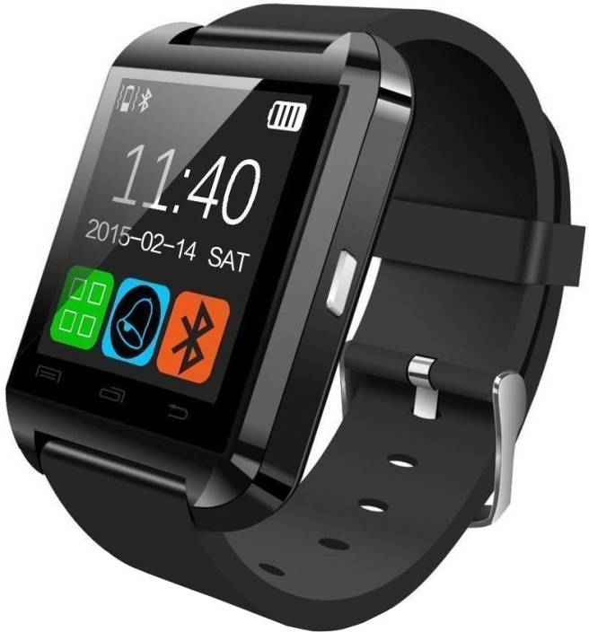
Presentationer/Presentation 10/u8-black-bingo-original-imaeeftzbhffagvw.jpeg
