jsjolund/sailoraid/Presentationer/Presentation 10/u8-black-bingo-original-imaeeftzbhffagvw.jpg

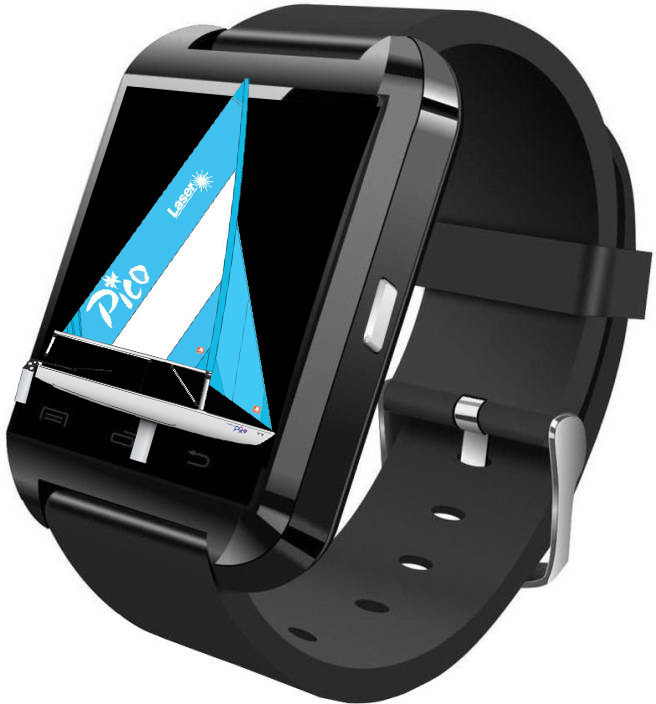
Presentationer/Presentation 10/u8-black-bingo-original-imaeeftzbhffagvw.jpg
