jsjolund/sailoraid/Presentationer/Presentation 10/Untitled-1.png

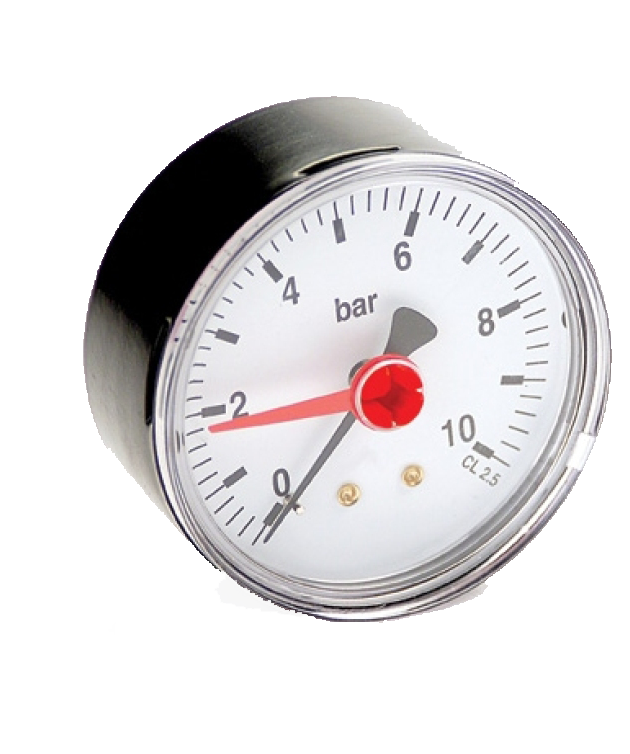
Presentationer/Presentation 10/Untitled-1.png
