jsjolund/sailoraid/Presentationer/Presentation 10/WONDERBOOM-Waterproof-Speaker-03.jpg

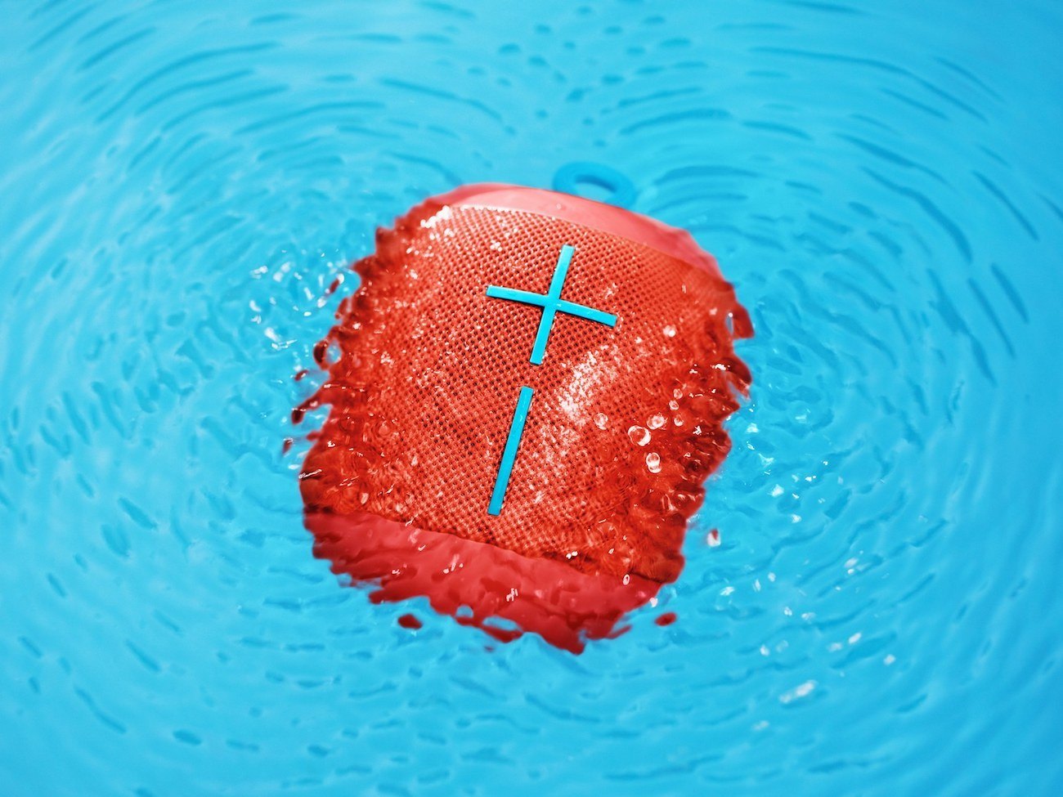
Presentationer/Presentation 10/WONDERBOOM-Waterproof-Speaker-03.jpg
