jsjolund/sailoraid/Presentationer/Presentation 12/balance.gif

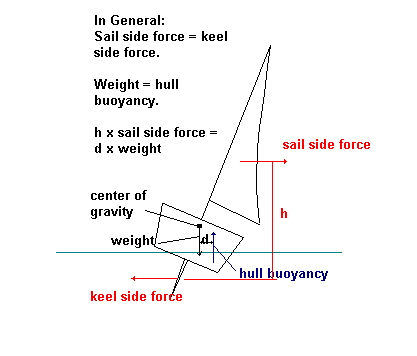
Presentationer/Presentation 12/balance.gif
