jsjolund/sailoraid/Presentationer/Presentation 12/course7.gif

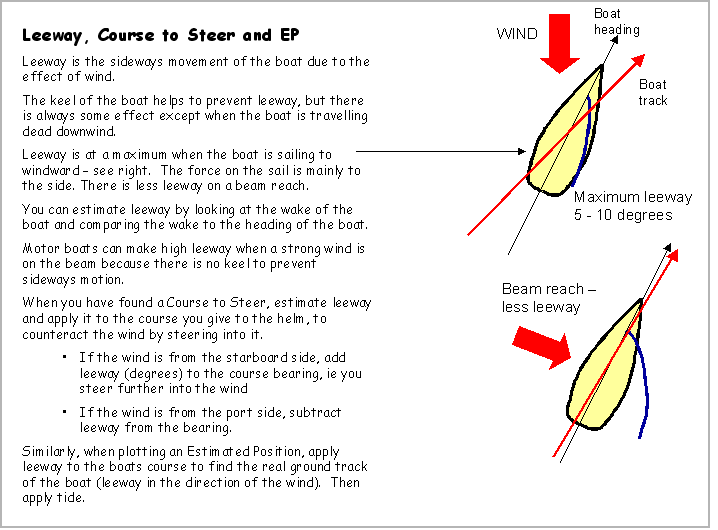
Presentationer/Presentation 12/course7.gif
