jsjolund/sailoraid/Presentationer/Presentation 12/course7.jpg

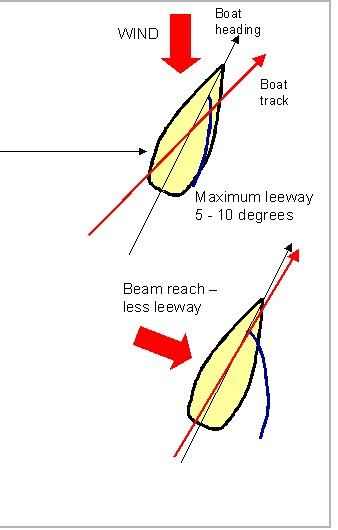
Presentationer/Presentation 12/course7.jpg
