jsjolund/sailoraid/Presentationer/Presentation 12/f7c1cb341d84724d4c2da1846b82faef.jpg

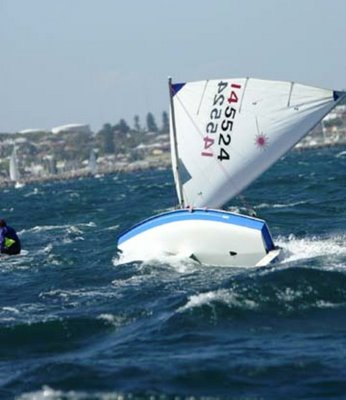
Presentationer/Presentation 12/f7c1cb341d84724d4c2da1846b82faef.jpg
