jsjolund/sailoraid/Presentationer/Presentation 12/hike3.gif

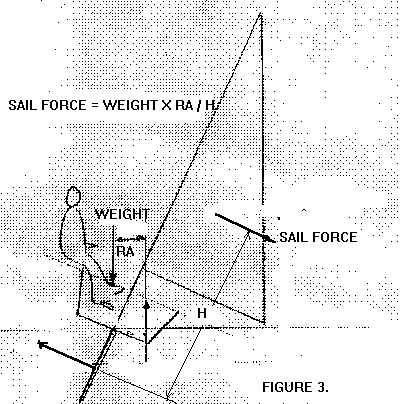
Presentationer/Presentation 12/hike3.gif
