jsjolund/sailoraid/Presentationer/Presentation 12/hiking.gif

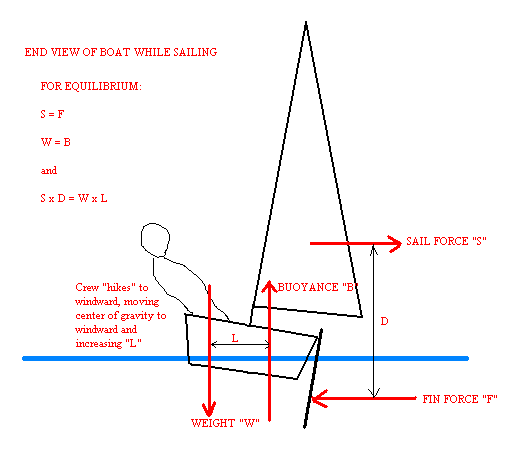
Presentationer/Presentation 12/hiking.gif
