jsjolund/sailoraid/Presentationer/Presentation 12/hydroptere2_0.jpg

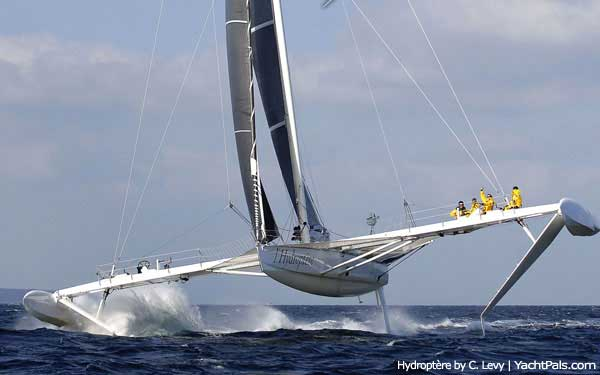
Presentationer/Presentation 12/hydroptere2_0.jpg
