jsjolund/sailoraid/Presentationer/Presentation 12/ladda ned.jpg

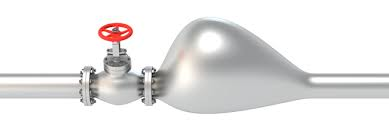
Presentationer/Presentation 12/ladda ned.jpg
