jsjolund/sailoraid/Presentationer/Presentation 12/ladda ned.png

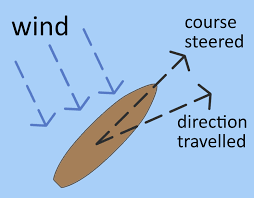
Presentationer/Presentation 12/ladda ned.png
