jsjolund/sailoraid/Presentationer/Presentation 12/leeway.jpg

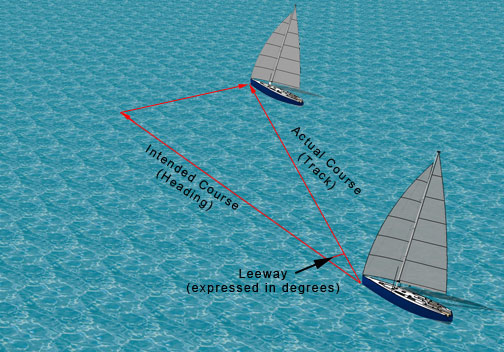
Presentationer/Presentation 12/leeway.jpg
