jsjolund/sailoraid/Presentationer/Presentation 12/Mark-Denzer-Laser-2.jpg

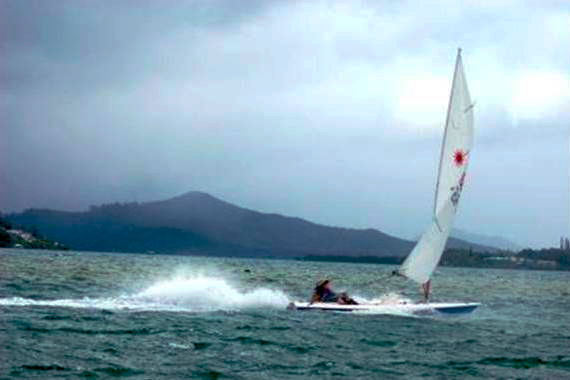
Presentationer/Presentation 12/Mark-Denzer-Laser-2.jpg
