jsjolund/sailoraid/Presentationer/Presentation 12/Screenshot_20171203-110926.png

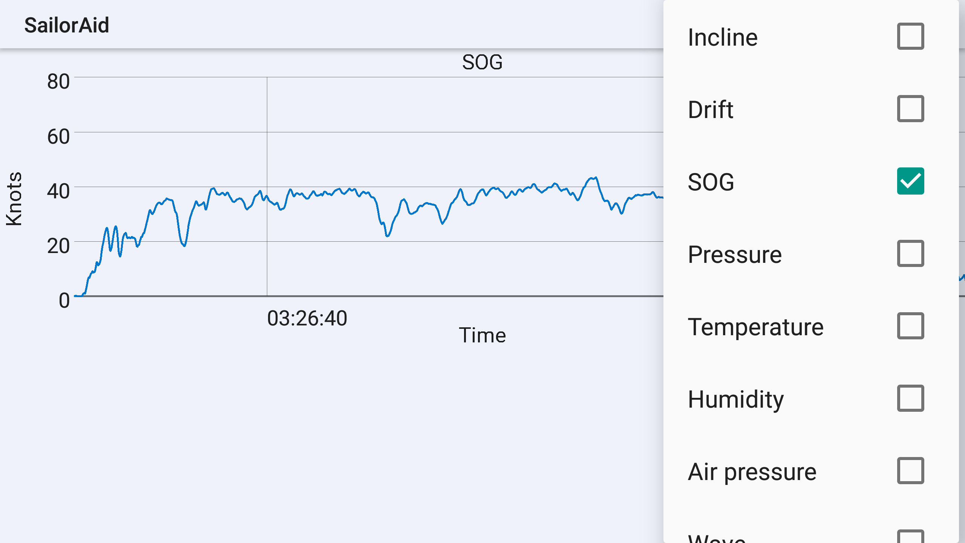
Presentationer/Presentation 12/Screenshot_20171203-110926.png
