jsjolund/sailoraid/Presentationer/Presentation 12/Screenshot_20171203-110933.png

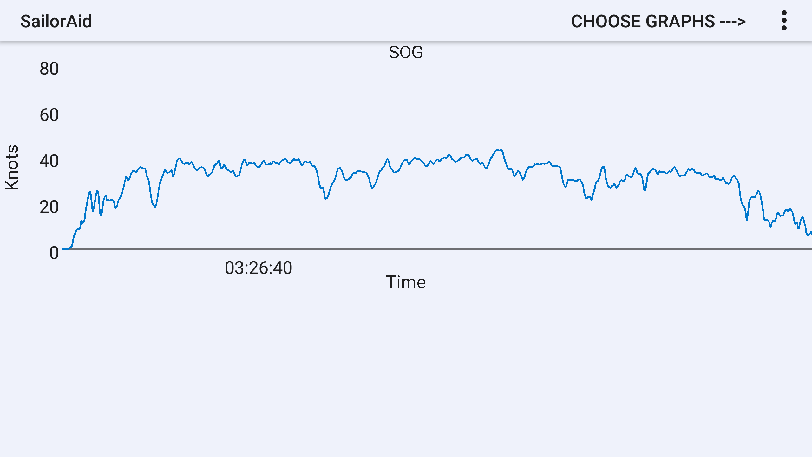
Presentationer/Presentation 12/Screenshot_20171203-110933.png
