jsjolund/sailoraid/Presentationer/Presentation 12/Untitled.jpg

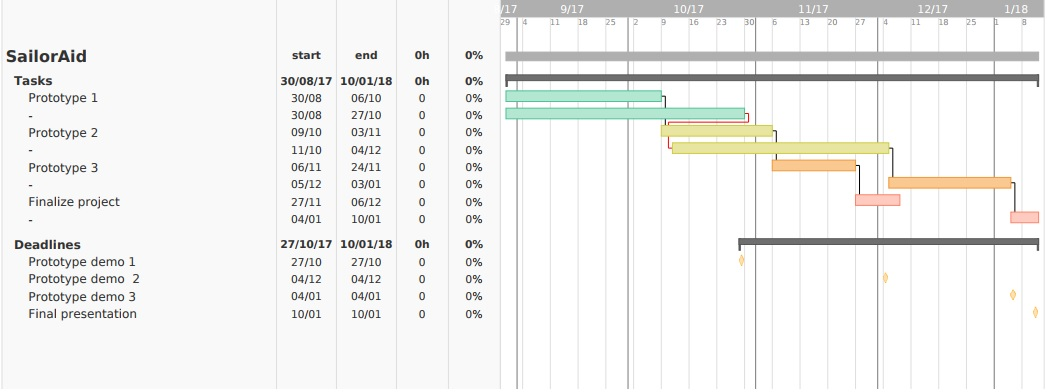
Presentationer/Presentation 12/Untitled.jpg
