jsjolund/sailoraid/Presentationer/Presentation 12/windward.jpg

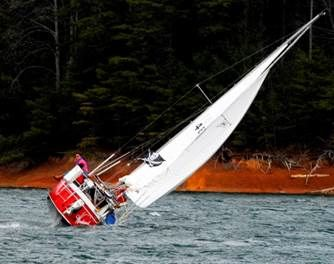
Presentationer/Presentation 12/windward.jpg
