jsjolund/sailoraid/Presentationer/Presentation 12/yandy86318.jpg

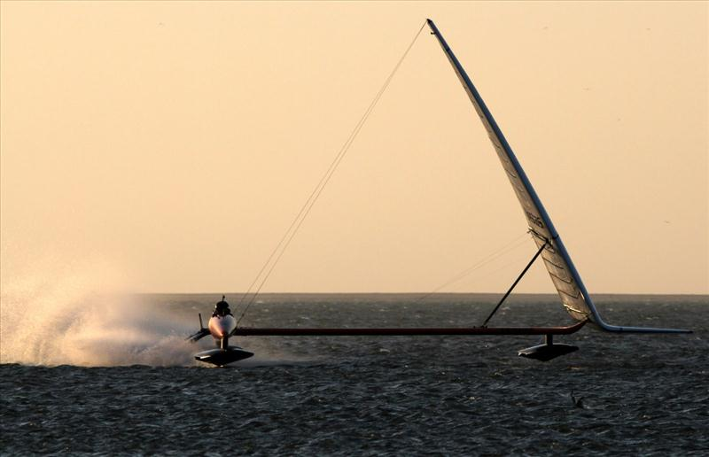
Presentationer/Presentation 12/yandy86318.jpg
