jsjolund/sailoraid/report/Figures/boat.png

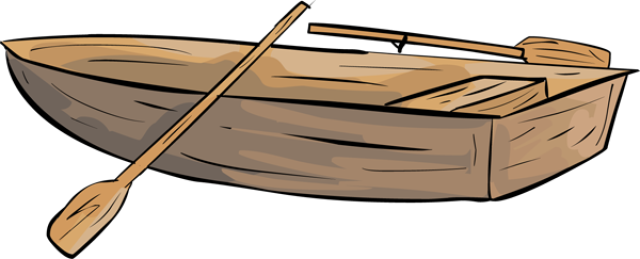
report/Figures/boat.png
