jsjolund/sailoraid/report/Figures/Capture.PNG

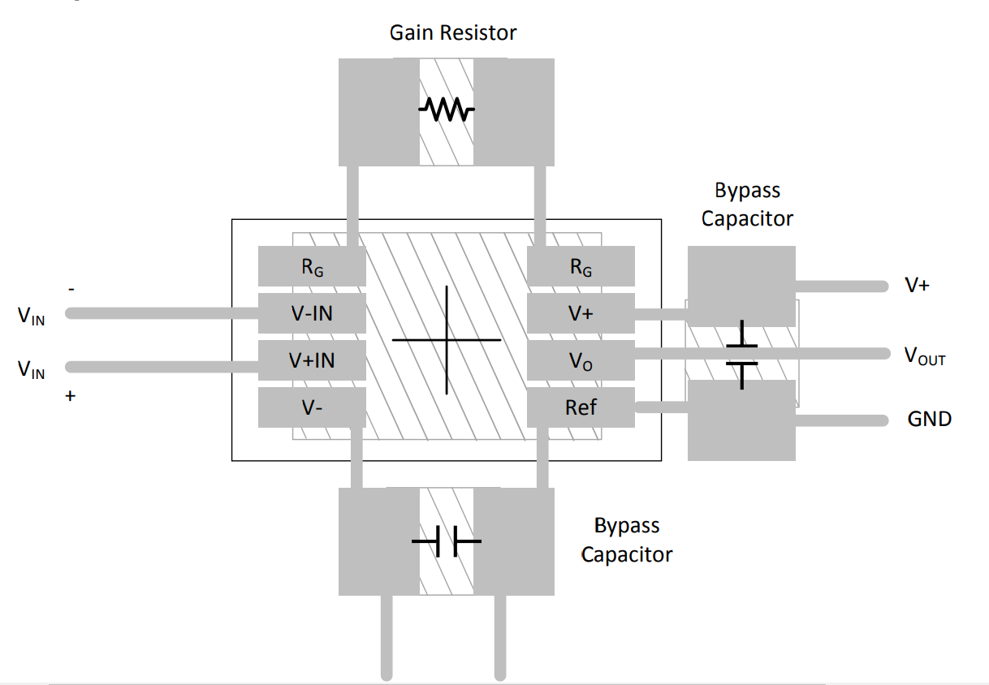
report/Figures/Capture.PNG
