jsjolund/sailoraid/report/Figures/EVA2235-H.jpg

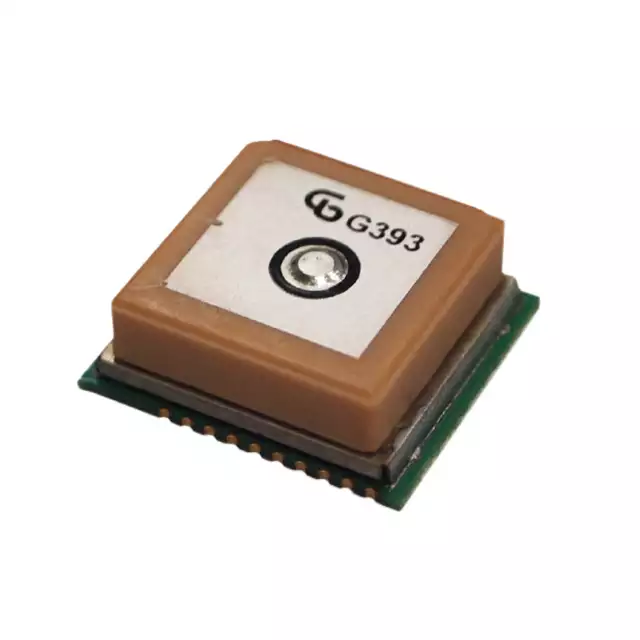
report/Figures/EVA2235-H.jpg
