jsjolund/sailoraid/report/Figures/INA126.png

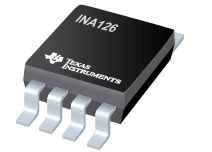
report/Figures/INA126.png
