jsjolund/sailoraid/report/Figures/missing.png

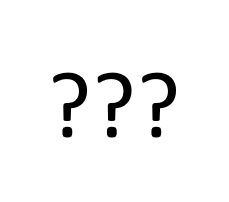
report/Figures/missing.png
