jsjolund/sailoraid/report/SourceFigures/Case_rev_1.png

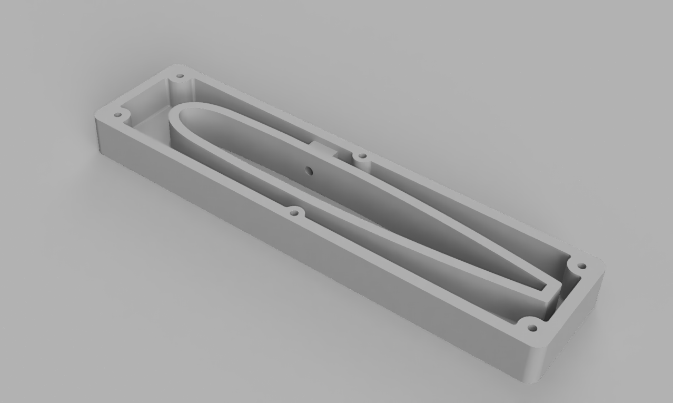
report/SourceFigures/Case_rev_1.png
