jsjolund/sailoraid/report/SourceFigures/Case_rev_2.png

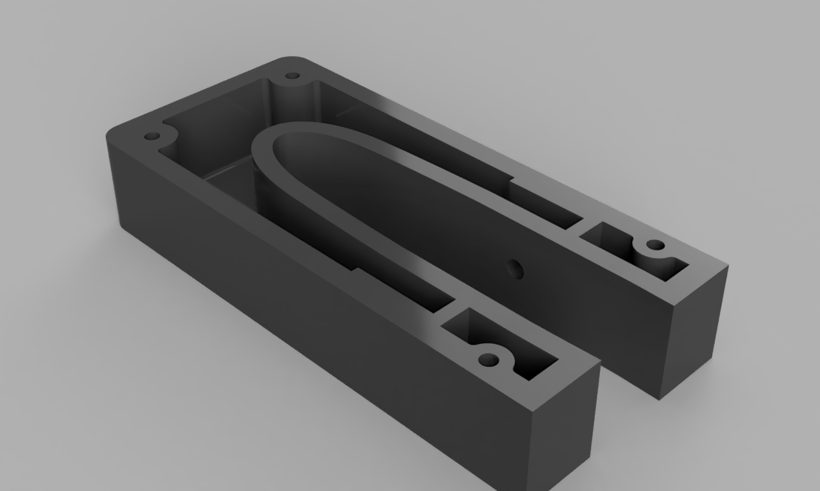
report/SourceFigures/Case_rev_2.png
