jsjolund/sailoraid/report/SourceFigures/Case_rev_3.png

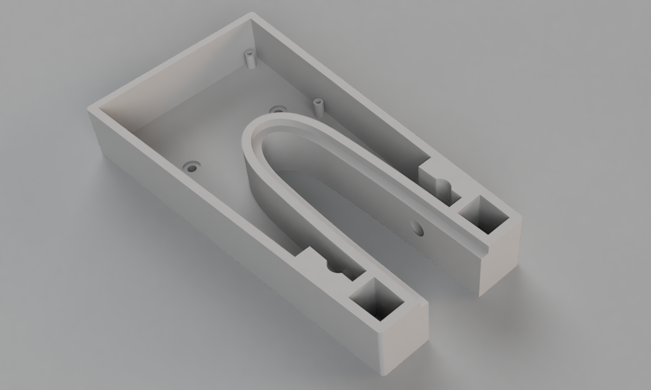
report/SourceFigures/Case_rev_3.png
