jsjolund/sailoraid/report/SourceFigures/Case_rev_4.png

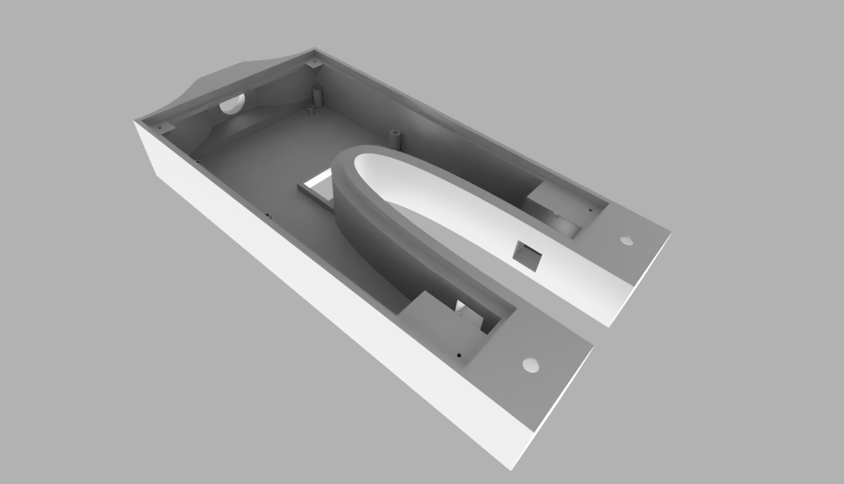
report/SourceFigures/Case_rev_4.png
