jsjolund/sailoraid/report/SourceFigures/Press_sens_prot_1.png

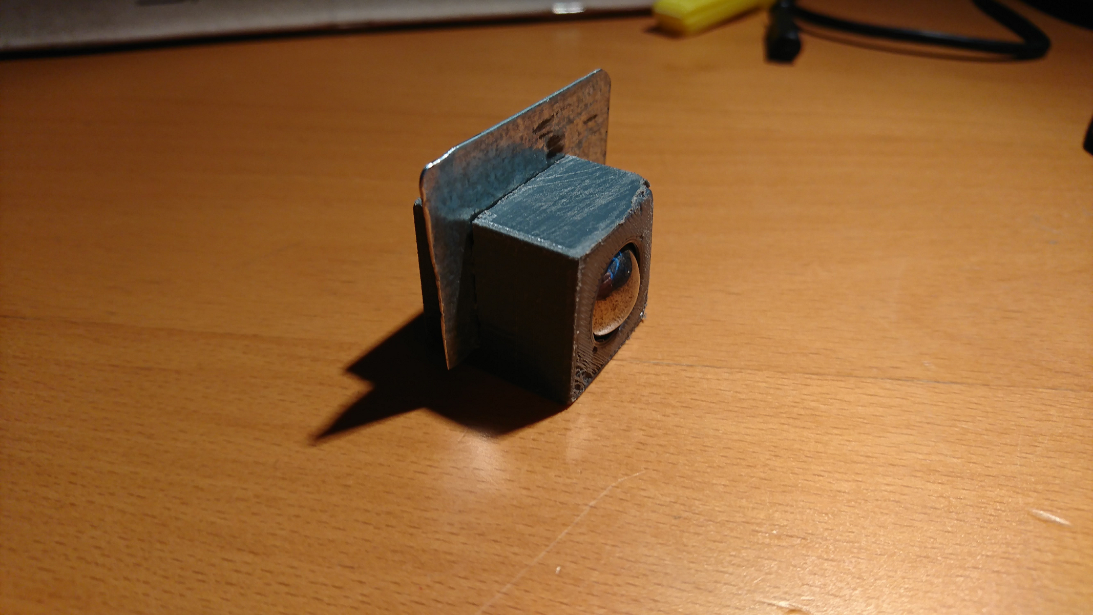
report/SourceFigures/Press_sens_prot_1.png
