jsjolund/sailoraid/report/SourceFigures/Prototyp_1.png

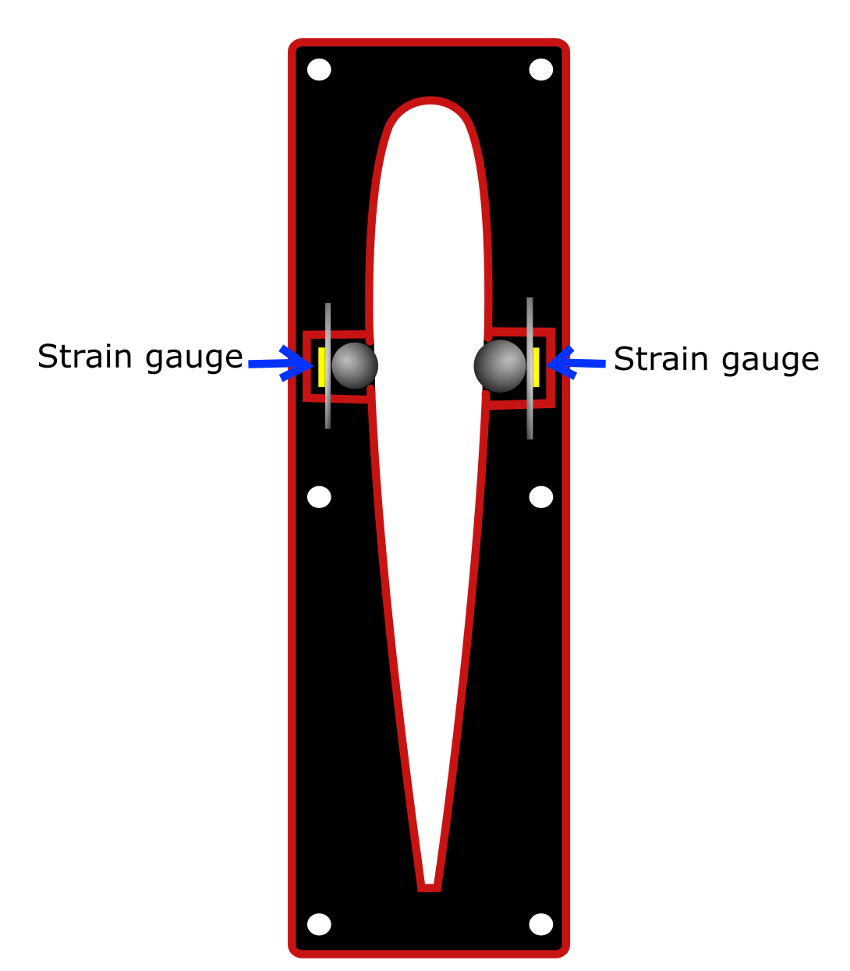
report/SourceFigures/Prototyp_1.png
