jsjolund/sailoraid/report/SourceFigures/stm32nucleo.jpg

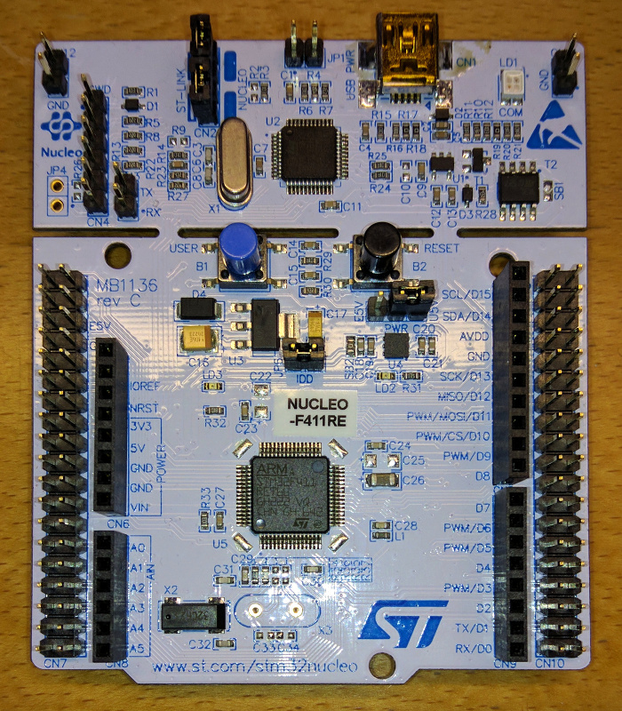
report/SourceFigures/stm32nucleo.jpg
