jsjolund/sailoraid/report/SourceFigures/wave.png

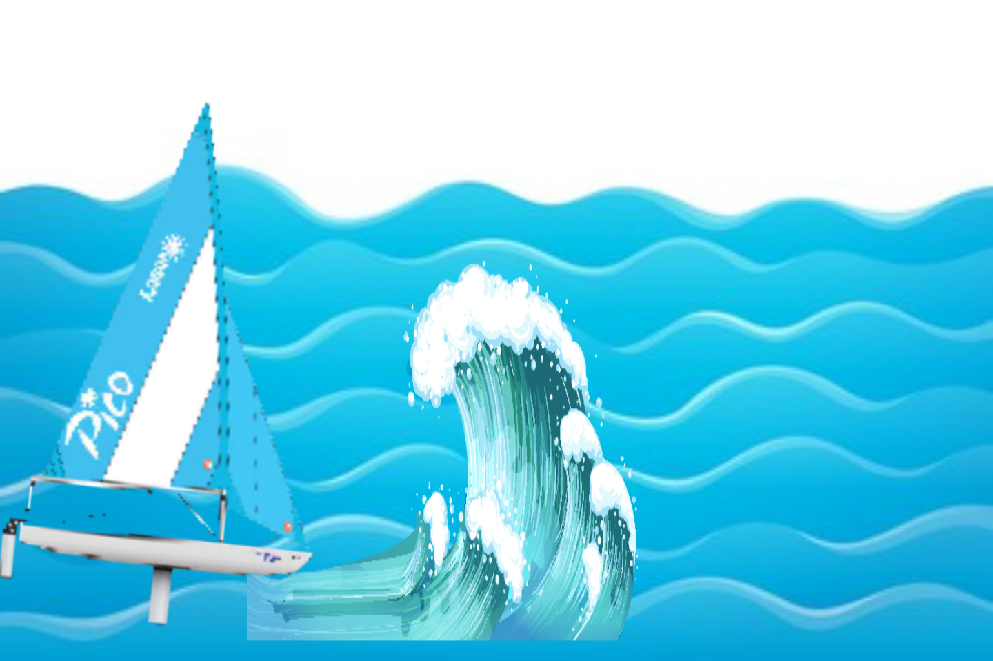
report/SourceFigures/wave.png
