jsjolund/sailoraid/report/SourceFigures/x-nucleo-iks01a2.jpg

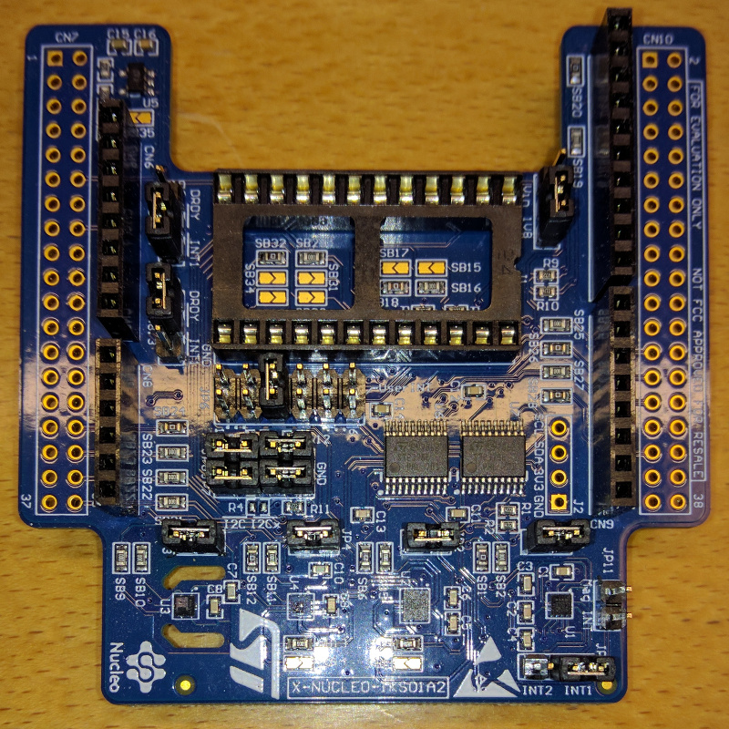
report/SourceFigures/x-nucleo-iks01a2.jpg
