jsjolund/sailoraid/Inc/x_nucleo_iks01a2.h

/**
  ******************************************************************************
  * @file    x_nucleo_iks01a2.h
  * @author  MEMS Application Team
  * @version V4.0.0
  * @date    1-May-2017
  * @brief   This file contains definitions for the x_nucleo_iks01a2.c
  ******************************************************************************
  * @attention
  *
  * <h2><center>&copy; COPYRIGHT(c) 2017 STMicroelectronics</center></h2>
  *
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
  ******************************************************************************
  */

/* Define to prevent recursive inclusion -------------------------------------*/
#ifndef __X_NUCLEO_IKS01A2_H
#define __X_NUCLEO_IKS01A2_H

#ifdef __cplusplus
extern "C" {
#endif



/* Includes ------------------------------------------------------------------*/

#ifdef USE_STM32F4XX_NUCLEO
#include "stm32f4xx_hal.h"
#endif

#ifdef USE_STM32L0XX_NUCLEO
#include "stm32l0xx_hal.h"
#endif

#ifdef USE_STM32L1XX_NUCLEO
#include "stm32l1xx_hal.h"
#endif

#ifdef USE_STM32L4XX_NUCLEO
#include "stm32l4xx_hal.h"
#endif

#include "accelerometer.h"
#include "gyroscope.h"
#include "magnetometer.h"
#include "humidity.h"
#include "temperature.h"
#include "pressure.h"

#include "main.h"

/** @addtogroup BSP BSP
 * @{
 */

/** @addtogroup X_NUCLEO_IKS01A2 X_NUCLEO_IKS01A2
 * @{
 */

/** @addtogroup X_NUCLEO_IKS01A2_IO IO
 * @{
 */

/** @addtogroup X_NUCLEO_IKS01A2_IO_Public_Constants Public constants
 * @{
 */

#define IKS01A2_HTS221_WHO_AM_I        (uint8_t)0xBC
#define IKS01A2_LPS22HB_WHO_AM_I       (uint8_t)0xB1
#define IKS01A2_LSM6DSL_WHO_AM_I       (uint8_t)0x6B
#define IKS01A2_LSM303AGR_ACC_WHO_AM_I (uint8_t)0x33
#define IKS01A2_LSM303AGR_MAG_WHO_AM_I (uint8_t)0x40
 
/* I2C clock speed configuration (in Hz) */
#if ((defined (USE_STM32F4XX_NUCLEO)) || (defined (USE_STM32L1XX_NUCLEO)))
#define NUCLEO_I2C_EXPBD_SPEED                         MAIN_I2C_SPEED
#endif /* USE_STM32F4XX_NUCLEO or USE_STM32L1XX_NUCLEO */

/* Timing samples for L0 with SYSCLK 32MHz set in SystemClock_Config() */
#if (defined (USE_STM32L0XX_NUCLEO))
#define NUCLEO_I2C_EXPBD_TIMING_100KHZ       0x10A13E56 /* Analog Filter ON, Rise Time 400ns, Fall Time 100ns */
#define NUCLEO_I2C_EXPBD_TIMING_400KHZ       0x00B1112E /* Analog Filter ON, Rise Time 250ns, Fall Time 100ns */
#endif /* USE_STM32L0XX_NUCLEO */

/* Timing samples for L4 with SYSCLK 80MHz set in SystemClock_Config() */
#if (defined (USE_STM32L4XX_NUCLEO))
#define NUCLEO_I2C_EXPBD_TIMING_400KHZ       0x10D1143A /* Analog Filter ON, Rise time 250ns, Fall Time 100ns */
#define NUCLEO_I2C_EXPBD_TIMING_1000KHZ      0x00D00E28 /* Analog Filter ON, Rise time 120ns, Fall time 25ns */
#endif /* USE_STM32L4XX_NUCLEO */

/* I2C peripheral configuration defines */
#define NUCLEO_I2C_EXPBD                            I2C1
#define NUCLEO_I2C_EXPBD_CLK_ENABLE()               __I2C1_CLK_ENABLE()
#define NUCLEO_I2C_EXPBD_SCL_SDA_GPIO_CLK_ENABLE()  __GPIOB_CLK_ENABLE()
#define NUCLEO_I2C_EXPBD_SCL_SDA_AF                 GPIO_AF4_I2C1
#define NUCLEO_I2C_EXPBD_SCL_SDA_GPIO_PORT          GPIOB
#define NUCLEO_I2C_EXPBD_SCL_PIN                    GPIO_PIN_8
#define NUCLEO_I2C_EXPBD_SDA_PIN                    GPIO_PIN_9

#define NUCLEO_I2C_EXPBD_FORCE_RESET()              __I2C1_FORCE_RESET()
#define NUCLEO_I2C_EXPBD_RELEASE_RESET()            __I2C1_RELEASE_RESET()

/* I2C interrupt requests */
#if ((defined (USE_STM32F4XX_NUCLEO)) || (defined (USE_STM32L1XX_NUCLEO)) || (defined (USE_STM32L4XX_NUCLEO)))
#define NUCLEO_I2C_EXPBD_EV_IRQn                    I2C1_EV_IRQn
#define NUCLEO_I2C_EXPBD_ER_IRQn                    I2C1_ER_IRQn
#endif

#if (defined (USE_STM32L0XX_NUCLEO))
#define NUCLEO_I2C_EXPBD_EV_IRQn                    I2C1_IRQn
#endif

/* Maximum Timeout values for flags waiting loops. These timeouts are not based
   on accurate values, they just guarantee that the application will not remain
   stuck if the I2C communication is corrupted.
   You may modify these timeout values depending on CPU frequency and application
   conditions (interrupts routines ...). */
#define NUCLEO_I2C_EXPBD_TIMEOUT_MAX    0x1000 /*<! The value of the maximal timeout for BUS waiting loops */

/* Definition for interrupt Pins */
#define LPS22H_INT1_O_GPIO_PORT           GPIOB
#define LPS22H_INT1_O_GPIO_CLK_ENABLE()   __GPIOB_CLK_ENABLE()
#define LPS22H_INT1_O_GPIO_CLK_DISABLE()  __GPIOB_CLK_DISABLE()
#define LPS22H_INT1_O_PIN                 GPIO_PIN_10

#if ((defined (USE_STM32F4XX_NUCLEO)) || (defined (USE_STM32L1XX_NUCLEO)) || (defined (USE_STM32L4XX_NUCLEO)))
#define LPS22H_INT1_O_EXTI_IRQn           EXTI15_10_IRQn
#endif

#if (defined (USE_STM32L0XX_NUCLEO))
#define LPS22H_INT1_O_EXTI_IRQn           EXTI4_15_IRQn
#endif

#define LSM6DSL_INT1_O_GPIO_PORT           GPIOB
#define LSM6DSL_INT1_O_GPIO_CLK_ENABLE()   __GPIOB_CLK_ENABLE()
#define LSM6DSL_INT1_O_GPIO_CLK_DISABLE()  __GPIOB_CLK_DISABLE()
#define LSM6DSL_INT1_O_PIN                 GPIO_PIN_5

#if ((defined (USE_STM32F4XX_NUCLEO)) || (defined (USE_STM32L1XX_NUCLEO)) || (defined (USE_STM32L4XX_NUCLEO)))
#define LSM6DSL_INT1_O_EXTI_IRQn           EXTI9_5_IRQn
#endif

#if (defined (USE_STM32L0XX_NUCLEO))
#define LSM6DSL_INT1_O_EXTI_IRQn           EXTI4_15_IRQn
#endif

#define M_INT1_O_GPIO_PORT           GPIOC
#define M_INT1_O_GPIO_CLK_ENABLE()   __GPIOC_CLK_ENABLE()
#define M_INT1_O_GPIO_CLK_DISABLE()  __GPIOC_CLK_DISABLE()
#define M_INT1_O_PIN                 GPIO_PIN_0

#if ((defined (USE_STM32F4XX_NUCLEO)) || (defined (USE_STM32L1XX_NUCLEO)) || (defined (USE_STM32L4XX_NUCLEO)))
#define M_INT1_O_EXTI_IRQn           EXTI0_IRQn
#endif

#if (defined (USE_STM32L0XX_NUCLEO))
#define M_INT1_O_EXTI_IRQn           EXTI0_1_IRQn
#endif

#define M_INT2_O_GPIO_PORT           GPIOC
#define M_INT2_O_GPIO_CLK_ENABLE()   __GPIOC_CLK_ENABLE()
#define M_INT2_O_GPIO_CLK_DISABLE()  __GPIOC_CLK_DISABLE()
#define M_INT2_O_PIN                 GPIO_PIN_1

#if ((defined (USE_STM32F4XX_NUCLEO)) || (defined (USE_STM32L1XX_NUCLEO)) || (defined (USE_STM32L4XX_NUCLEO)))
#define M_INT2_O_EXTI_IRQn           EXTI1_IRQn
#endif

#if (defined (USE_STM32L0XX_NUCLEO))
#define M_INT2_O_EXTI_IRQn           EXTI0_1_IRQn
#endif

#define LSM6DSL_INT2_O_GPIO_PORT           GPIOB
#define LSM6DSL_INT2_O_GPIO_CLK_ENABLE()   __GPIOB_CLK_ENABLE()
#define LSM6DSL_INT2_O_GPIO_CLK_DISABLE()  __GPIOB_CLK_DISABLE()
#define LSM6DSL_INT2_O_PIN                 GPIO_PIN_4

#if ((defined (USE_STM32F4XX_NUCLEO)) || (defined (USE_STM32L1XX_NUCLEO)) || (defined (USE_STM32L4XX_NUCLEO)))
#define LSM6DSL_INT2_O_EXTI_IRQn           EXTI4_IRQn
#endif

#if (defined (USE_STM32L0XX_NUCLEO))
#define LSM6DSL_INT2_O_EXTI_IRQn           EXTI4_15_IRQn
#endif

// ready for use
#define USER_INT_O_GPIO_PORT           GPIOA
#define USER_INT_O_GPIO_CLK_ENABLE()   __GPIOA_CLK_ENABLE()
#define USER_INT_O_GPIO_CLK_DISABLE()  __GPIOA_CLK_DISABLE()
#define USER_INT_O_PIN                 GPIO_PIN_10

#if ((defined (USE_STM32F4XX_NUCLEO)) || (defined (USE_STM32L1XX_NUCLEO)) || (defined (USE_STM32L4XX_NUCLEO)))
#define USER_INT_O_EXTI_IRQn           EXTI15_10_IRQn
#endif

#if (defined (USE_STM32L0XX_NUCLEO))
#define USER_INT_O_EXTI_IRQn           EXTI4_15_IRQn
#endif

// ready for use
#define LSM303AGR_DRDY_O_GPIO_PORT           GPIOA
#define LSM303AGR_DRDY_O_GPIO_CLK_ENABLE()   __GPIOA_CLK_ENABLE()
#define LSM303AGR_DRDY_O_GPIO_CLK_DISABLE()  __GPIOA_CLK_DISABLE()
#define LSM303AGR_DRDY_O_PIN                 GPIO_PIN_4

#if ((defined (USE_STM32F4XX_NUCLEO)) || (defined (USE_STM32L1XX_NUCLEO)) || (defined (USE_STM32L4XX_NUCLEO)))
#define LSM303AGR_DRDY_O_EXTI_IRQn           EXTI4_IRQn
#endif

#if (defined (USE_STM32L0XX_NUCLEO))
#define LSM303AGR_DRDY_O_EXTI_IRQn           EXTI4_15_IRQn
#endif

// ready for use
#define LSM303AGR_INT_O_GPIO_PORT           GPIOB
#define LSM303AGR_INT_O_GPIO_CLK_ENABLE()   __GPIOB_CLK_ENABLE()
#define LSM303AGR_INT_O_GPIO_CLK_DISABLE()  __GPIOB_CLK_DISABLE()
#define LSM303AGR_INT_O_PIN                 GPIO_PIN_0

#if ((defined (USE_STM32F4XX_NUCLEO)) || (defined (USE_STM32L1XX_NUCLEO)) || (defined (USE_STM32L4XX_NUCLEO)))
#define LSM303AGR_INT_O_EXTI_IRQn           EXTI0_IRQn
#endif

#if (defined (USE_STM32L0XX_NUCLEO))
#define LSM303AGR_INT_O_EXTI_IRQn           EXTI0_1_IRQn
#endif

/**
  * @}
  */

/** @addtogroup X_NUCLEO_IKS01A2_IO_Public_FunctionPrototypes Public function prototypes
 * @{
 */

DrvStatusTypeDef Sensor_IO_Init( void );
DrvStatusTypeDef LSM6DSL_Sensor_IO_ITConfig( void );
DrvStatusTypeDef LPS22HB_Sensor_IO_ITConfig( void );

/**
  * @}
  */

/**
  * @}
  */

/**
  * @}
  */

/**
  * @}
  */

#ifdef __cplusplus
}
#endif

#endif /* __X_NUCLEO_IKS01A2_H */

/************************ (C) COPYRIGHT STMicroelectronics *****END OF FILE****/
