jsjolund/sailoraid/Inc/shell.h

/*
 * shell.h
 *
 *  Created on: Sep 24, 2017
 *      Author: jsjolund
 */

#ifndef SHELL_H_
#define SHELL_H_

#include <stdio.h>
#include <stdlib.h>
#include <string.h>

#include "main.h"
#include "serial.h"
#include "hal_types.h"

void ShellExecute(char* string);

#endif /* SHELL_H_ */
